akkdong/FlightComputer/doc/LCD/5inch-HDMI-LCD-B-size.jpg

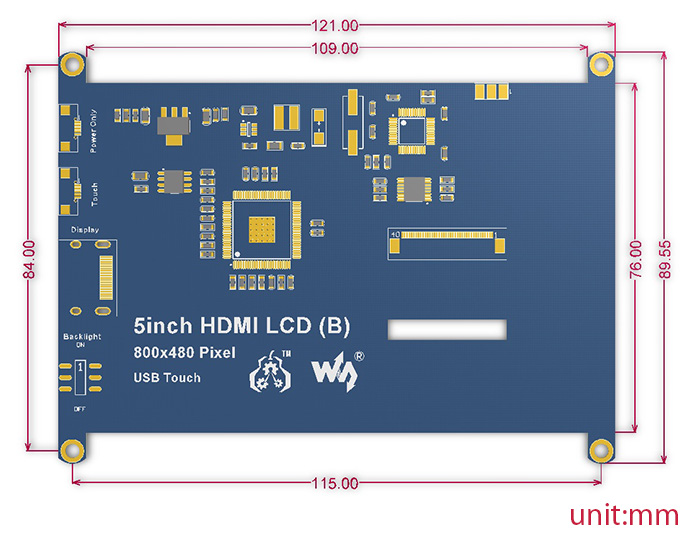
doc/LCD/5inch-HDMI-LCD-B-size.jpg
