akkdong/FlightComputer/hw/case/FlightComputer-Extra-Outline.dxf

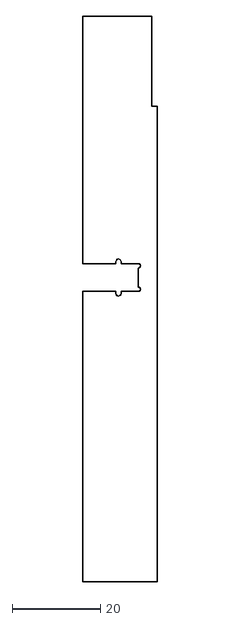
[picture p28: CAD file, 2020-10-16]
hw/case/FlightComputer-Extra-Outline.dxf
16.9 x 128.0
