akkdong/FlightComputer/hw/case/FlightComputer-Keypad-Parts.dxf

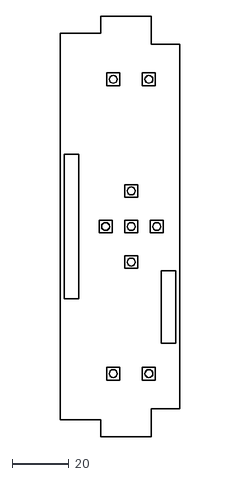
[picture p29: CAD file, 2020-10-16]
hw/case/FlightComputer-Keypad-Parts.dxf
42.0 x 148.0
