akkdong/FlightComputer/hw/case/FlightComputer-Dimension-Main.pdf

0 118.96 32.6

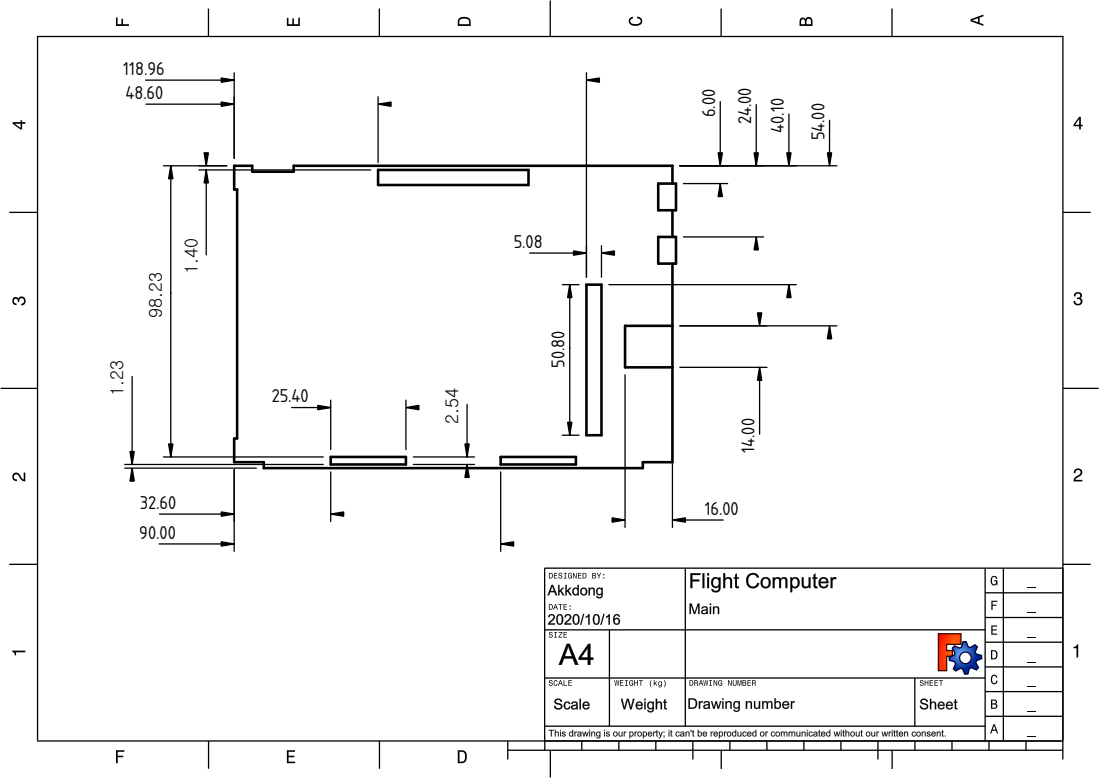
[picture p48: page 1]
