akkdong/FlightComputer/hw/case/FlightComputer-Dimension-Extra.pdf

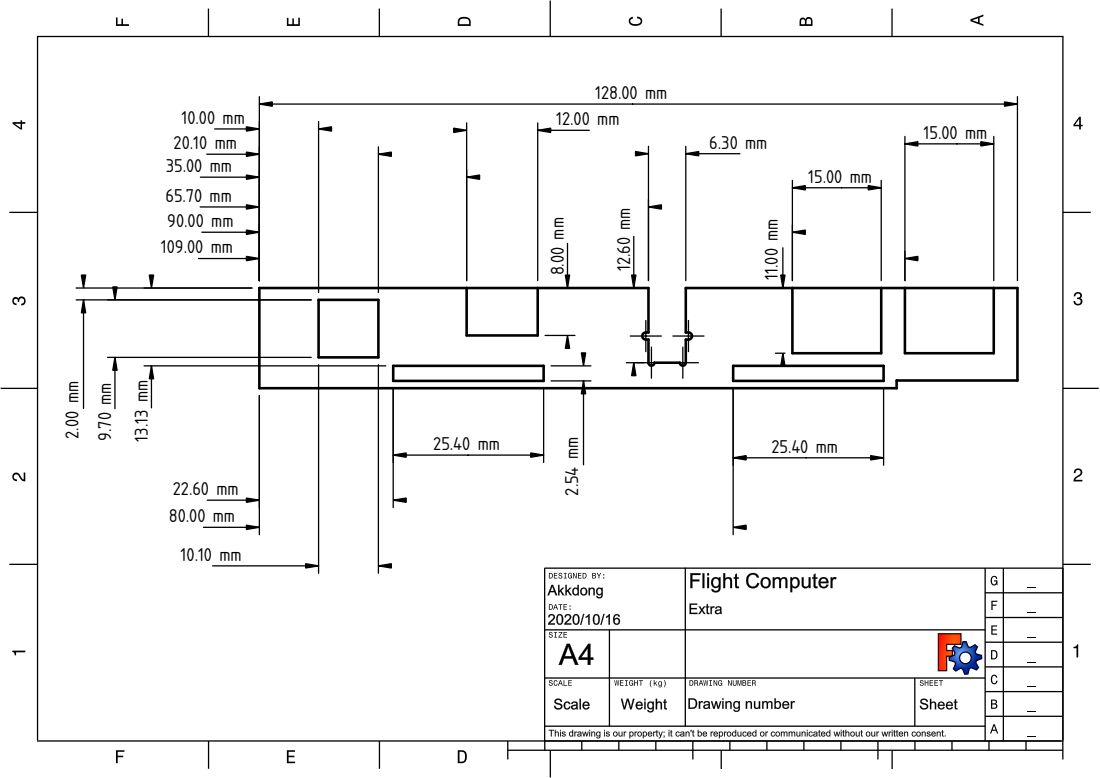
[picture p49: page 1]
