akkdong/FlightComputer/hw/case/FlightComputer-Dimension-Keypad.pdf

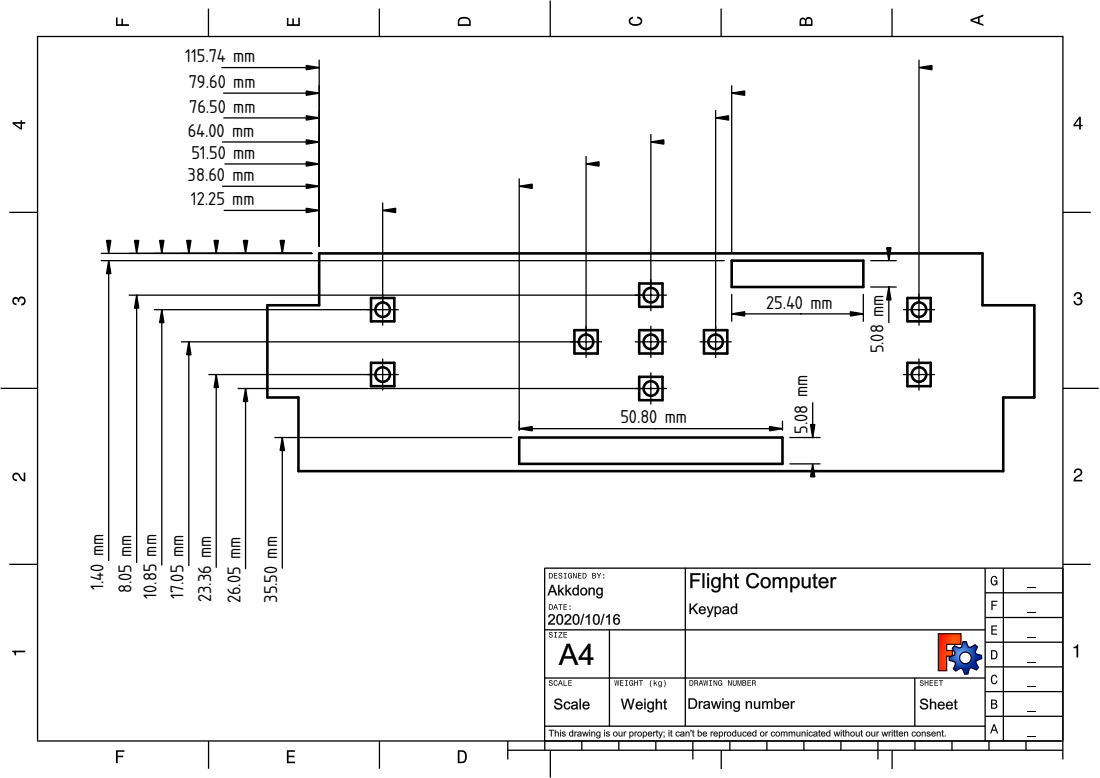
[picture p50: page 1]
