akkdong/FlightComputer/doc/LCD/5inch-hdmi-lcd-&-5inch-hdmi-lcd-b-panel-dimension.pdf

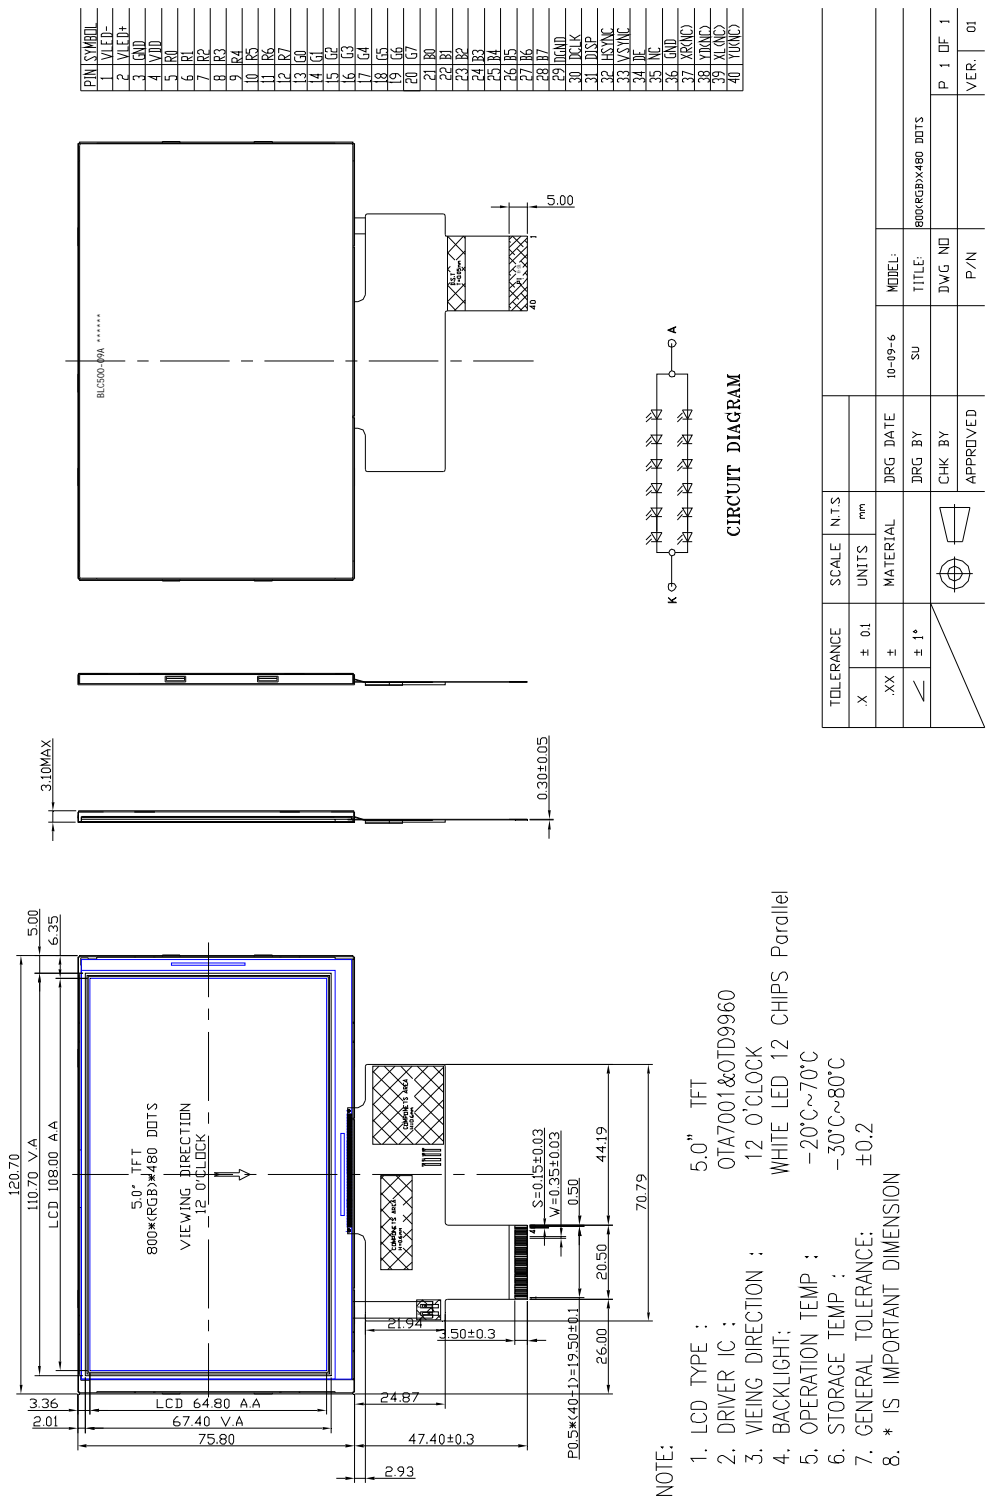
[picture p51: page 1]
BLC500-09A ******
