akkdong/FlightComputer/hw/rev1/FlightComputer/FlightComputer.pdf

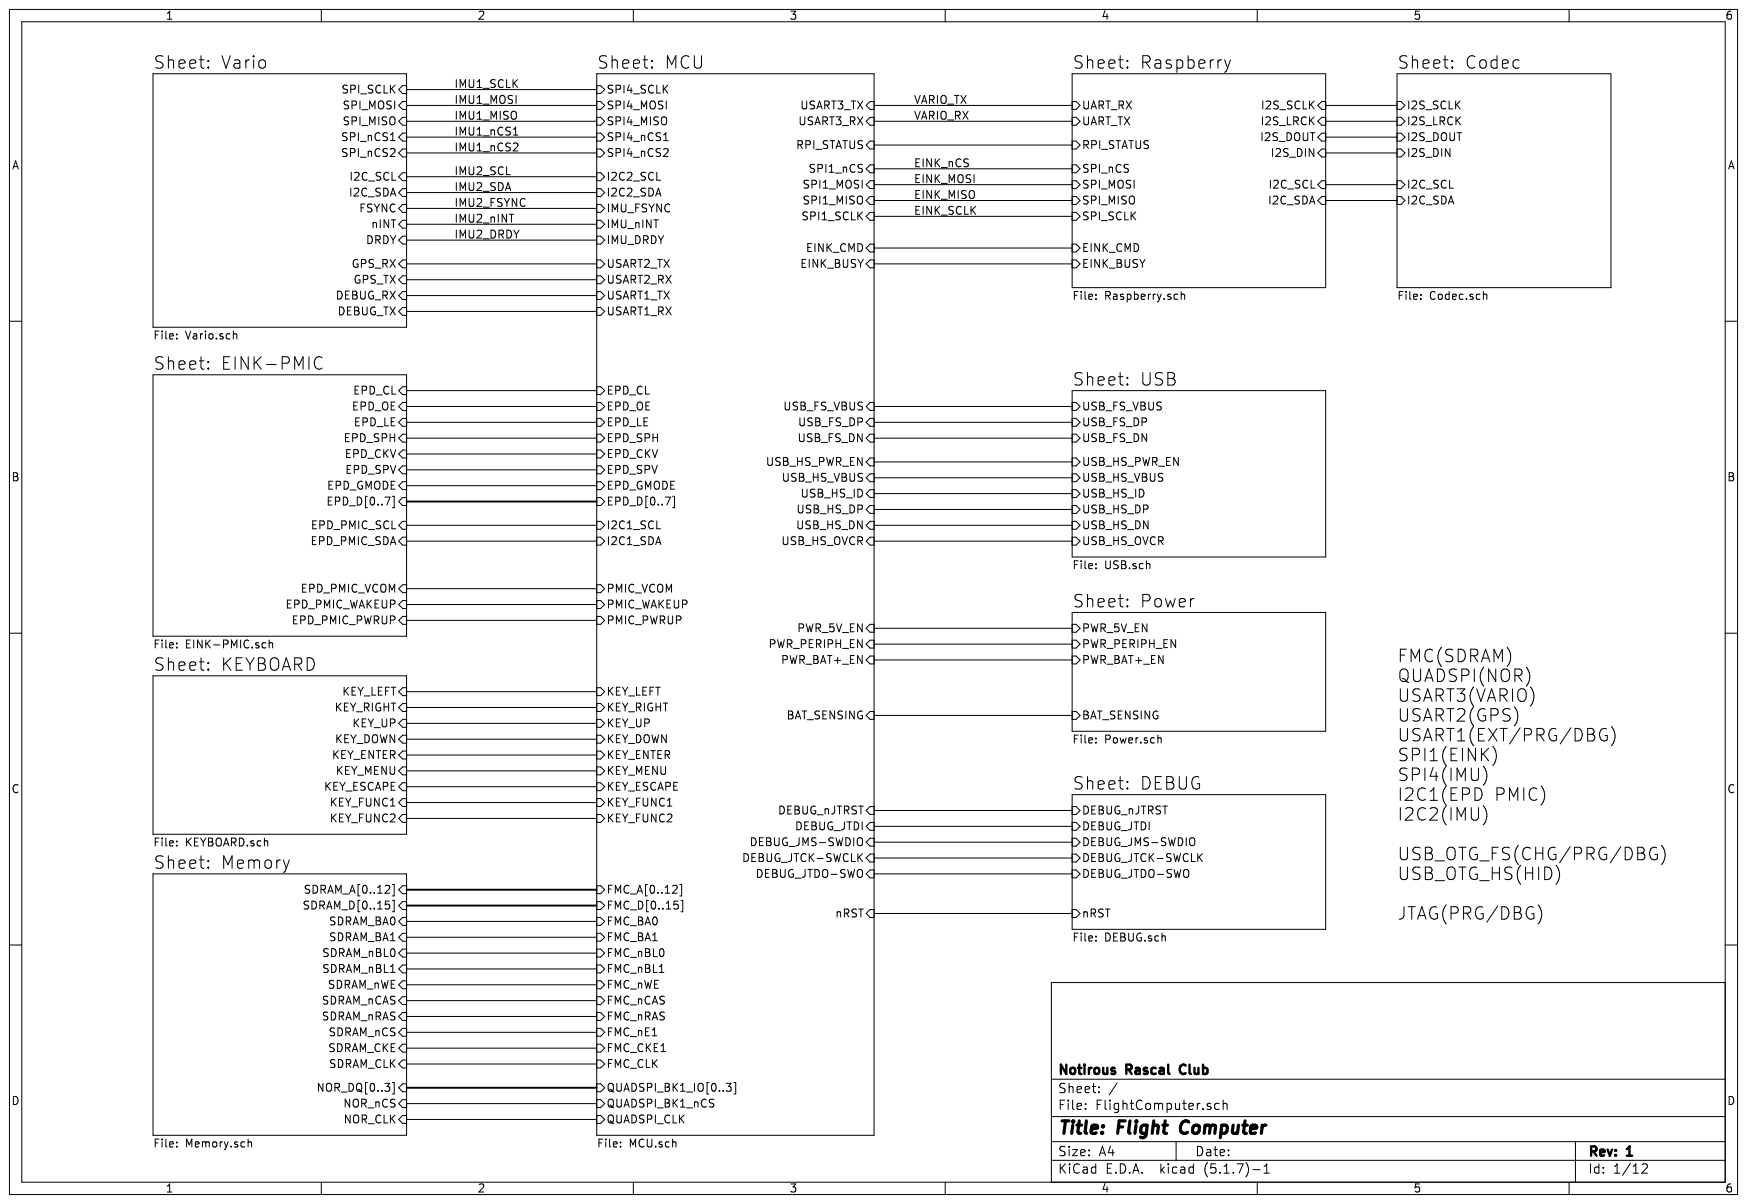
[picture p52: page 1]

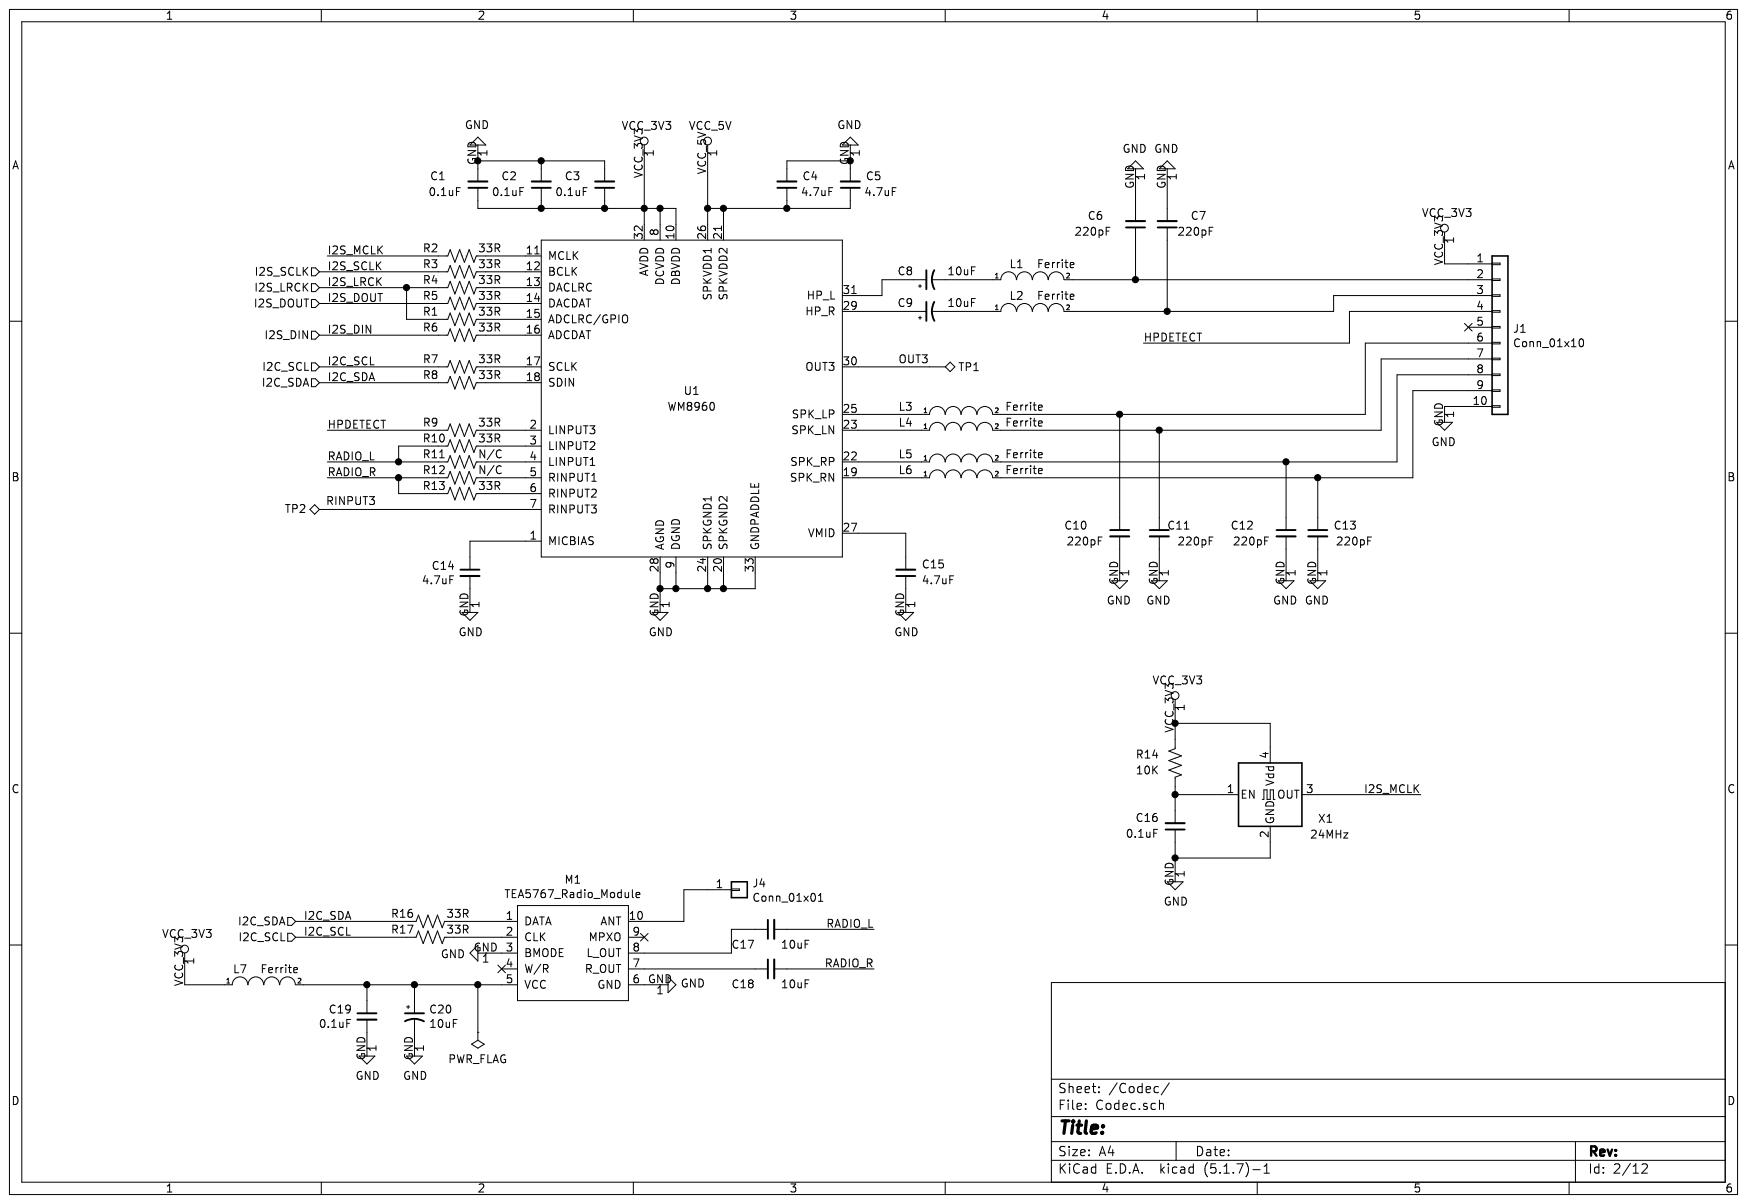
[picture p53: page 2]

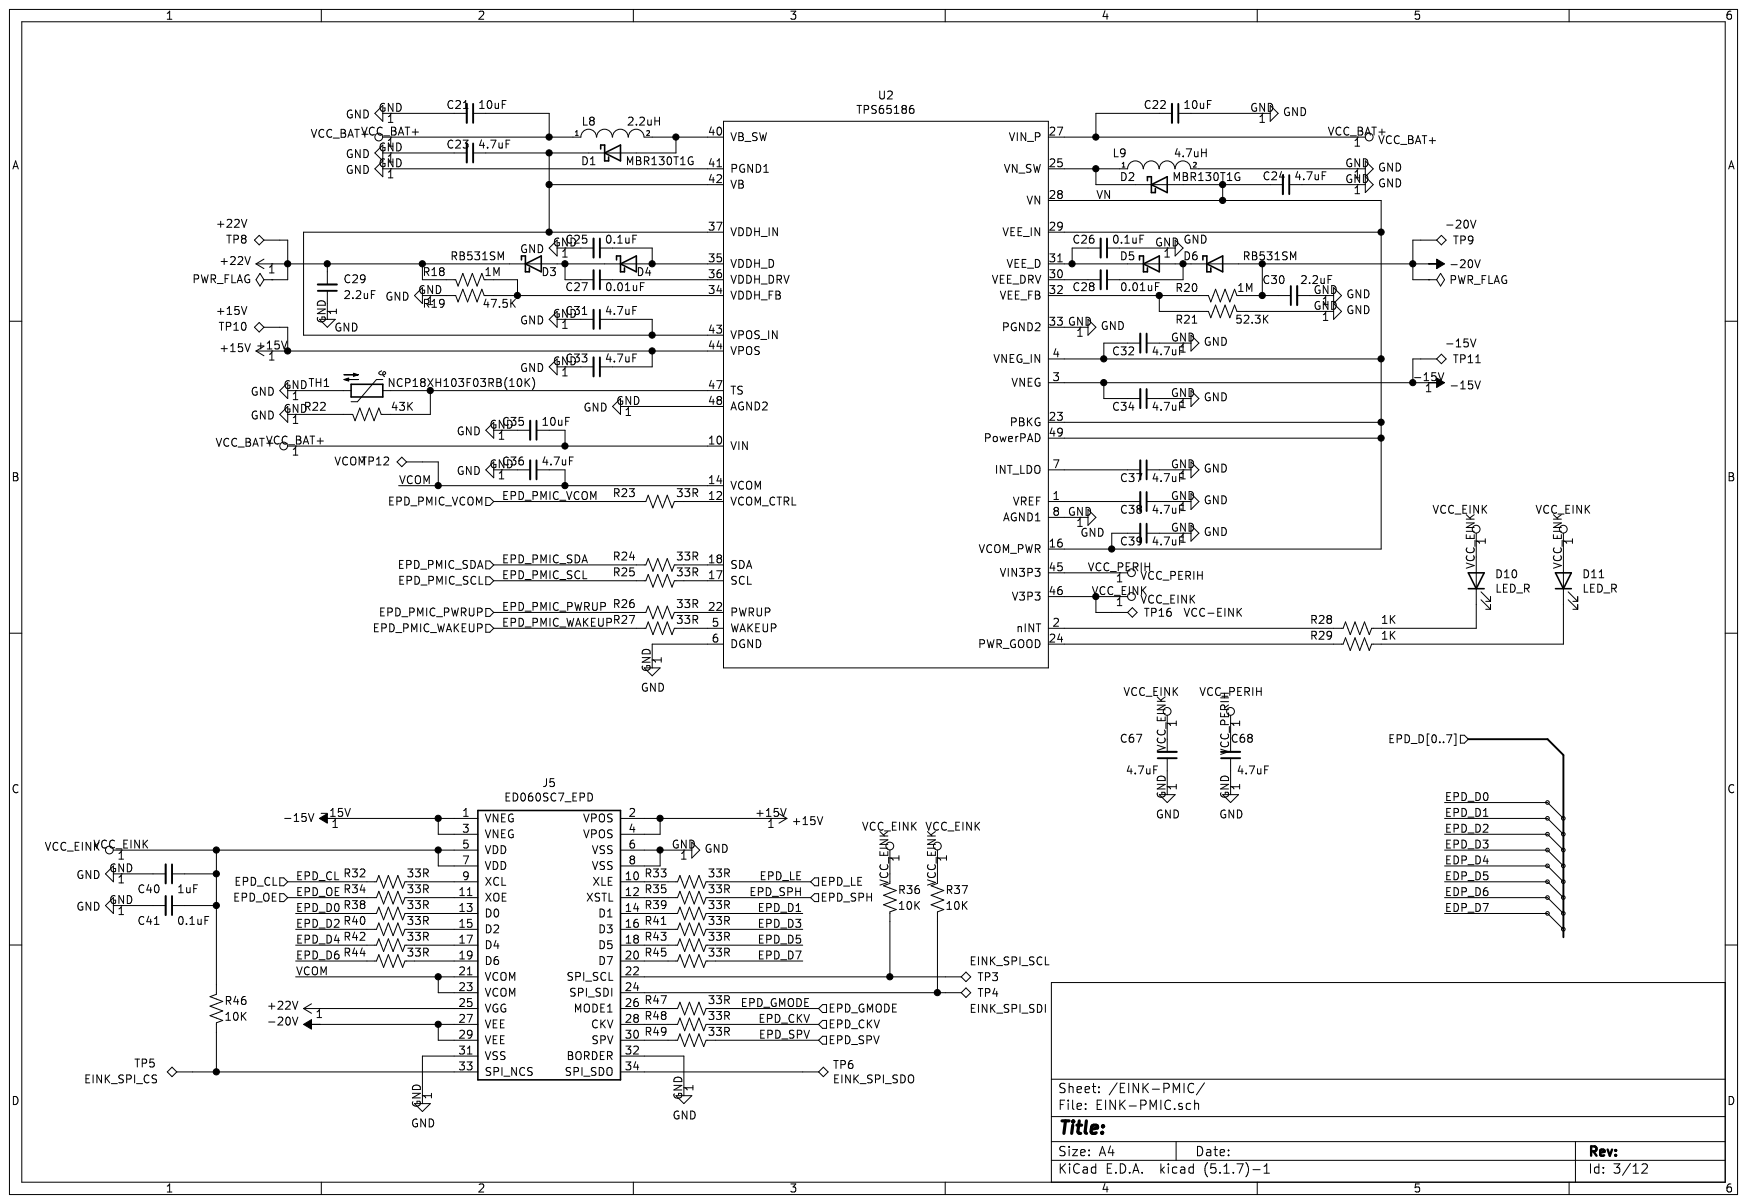
[picture p54: page 3]

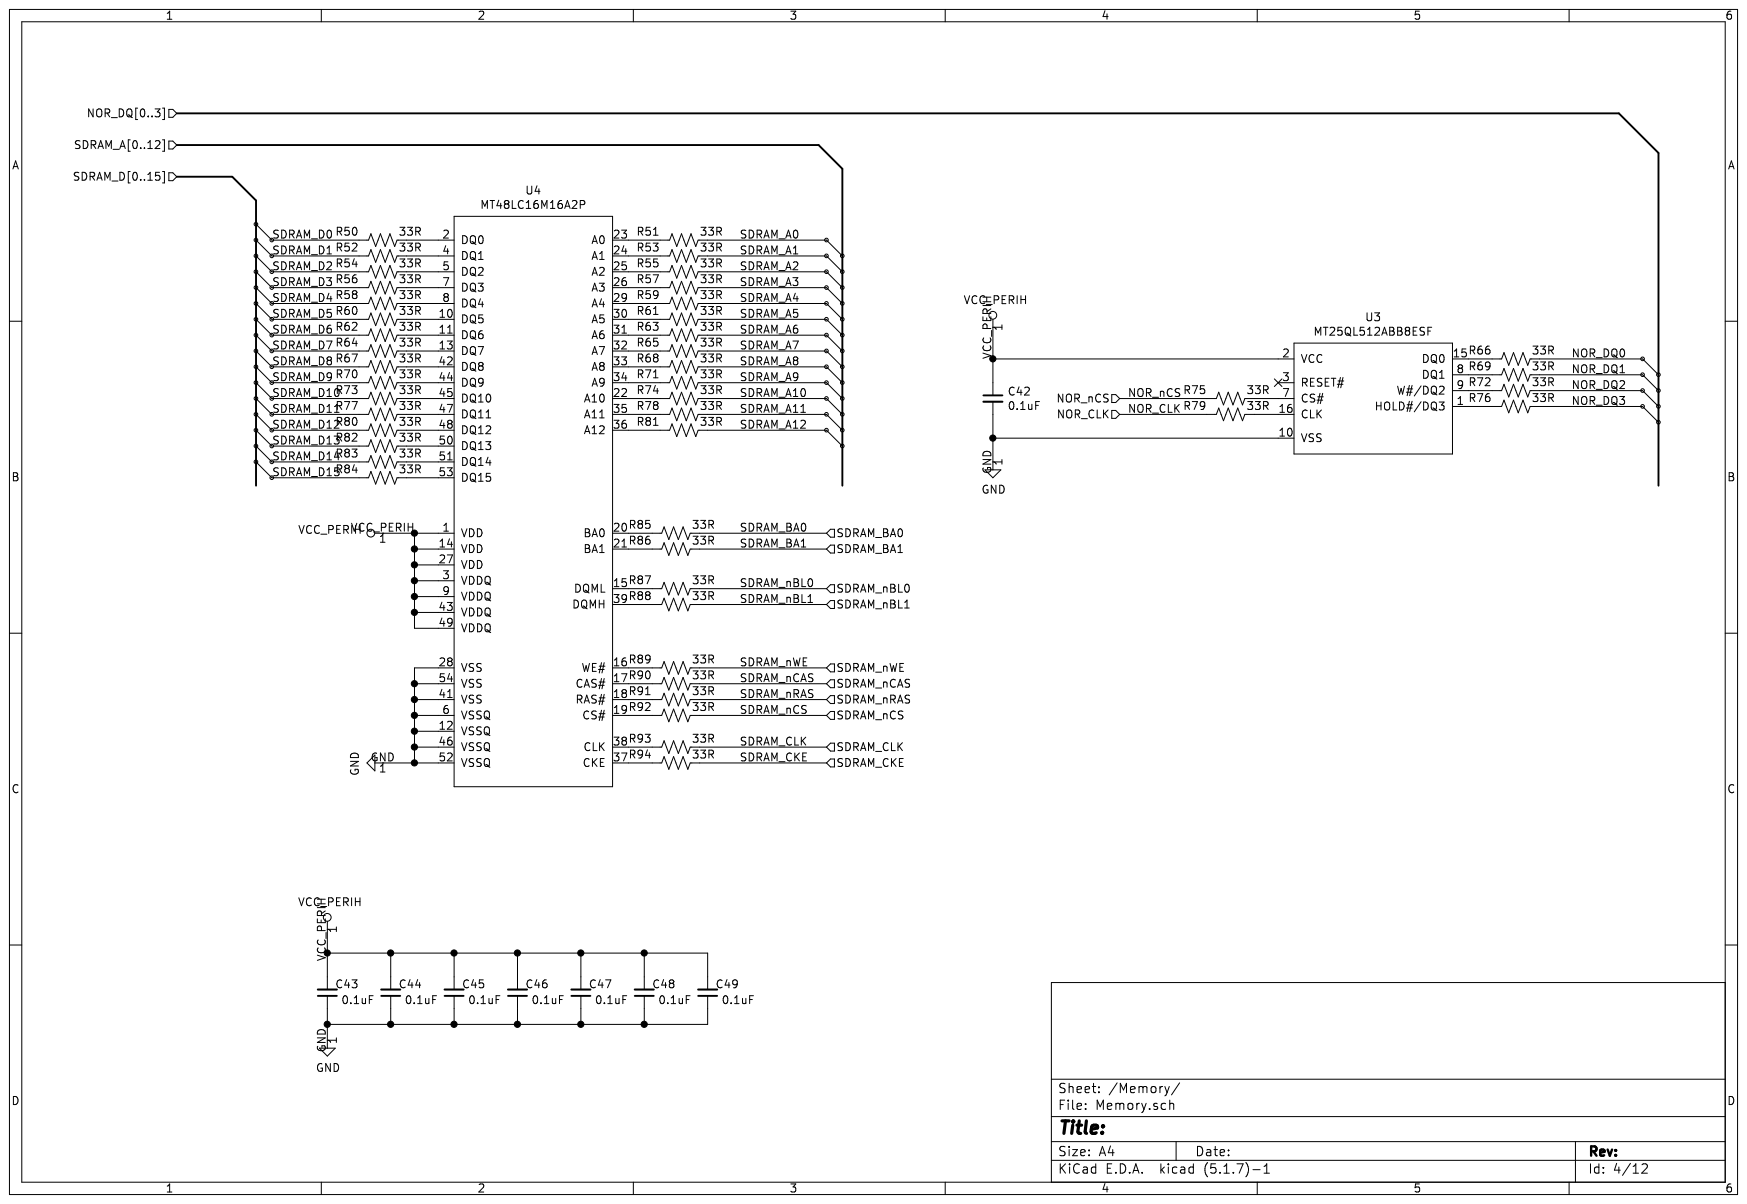
[picture p55: page 4]

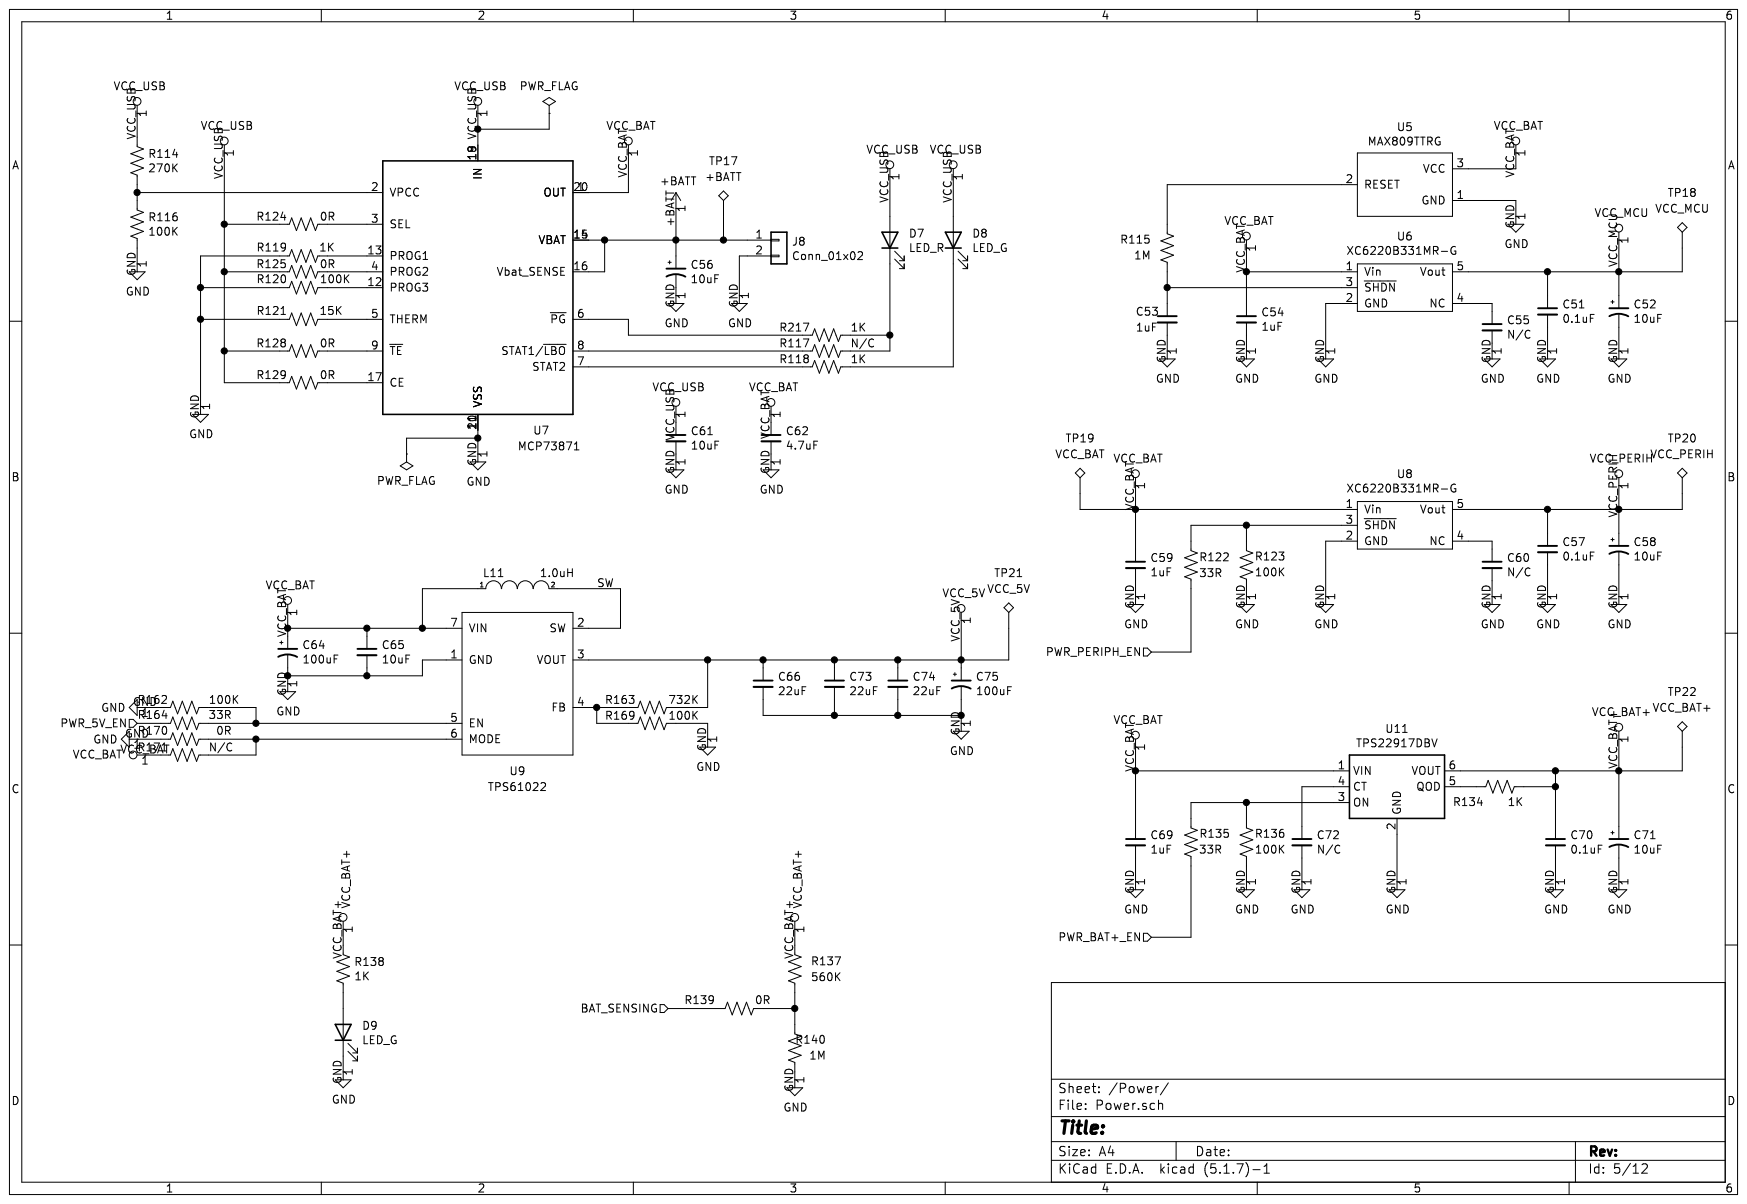
[picture p56: page 5]

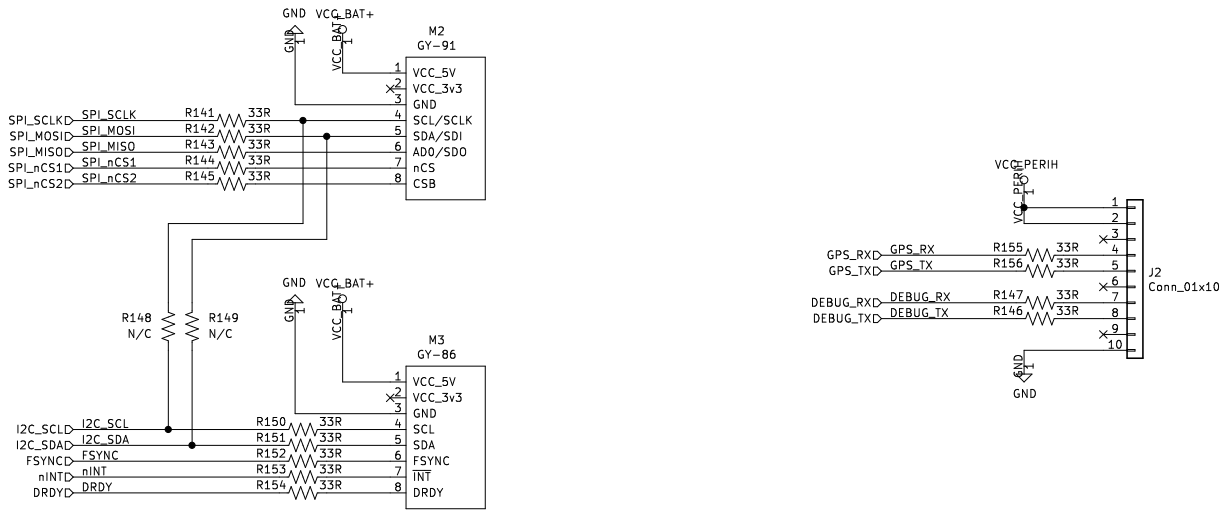
[picture p57: page 6]

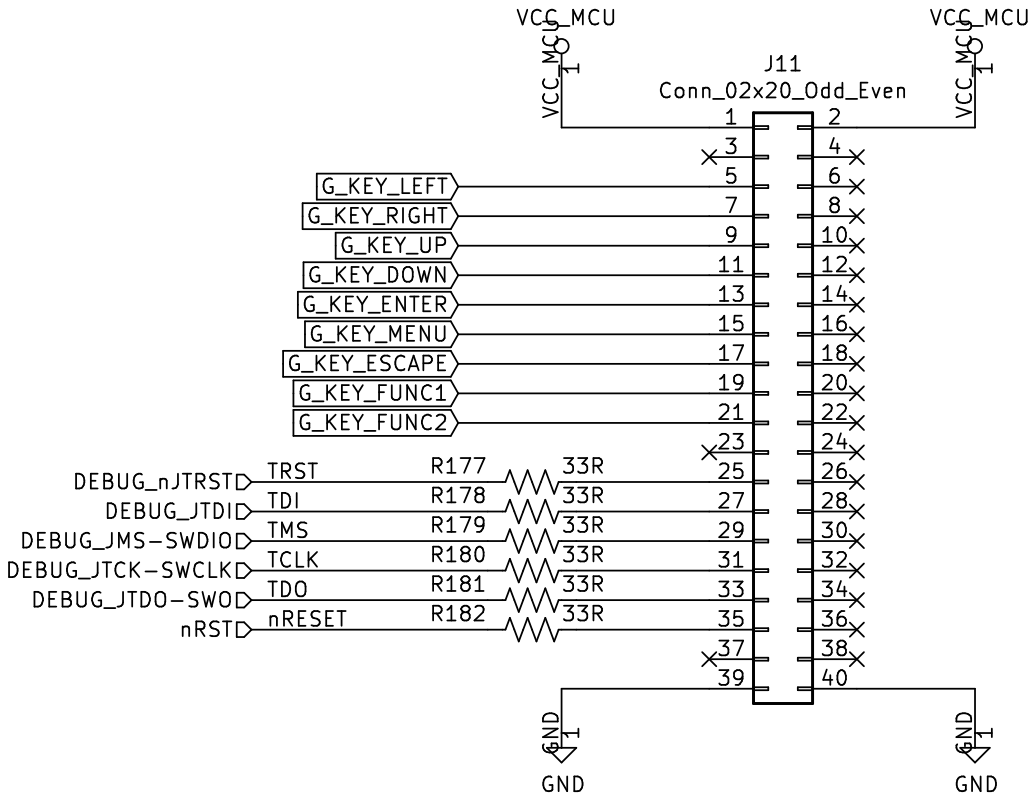
[picture p58: page 7]

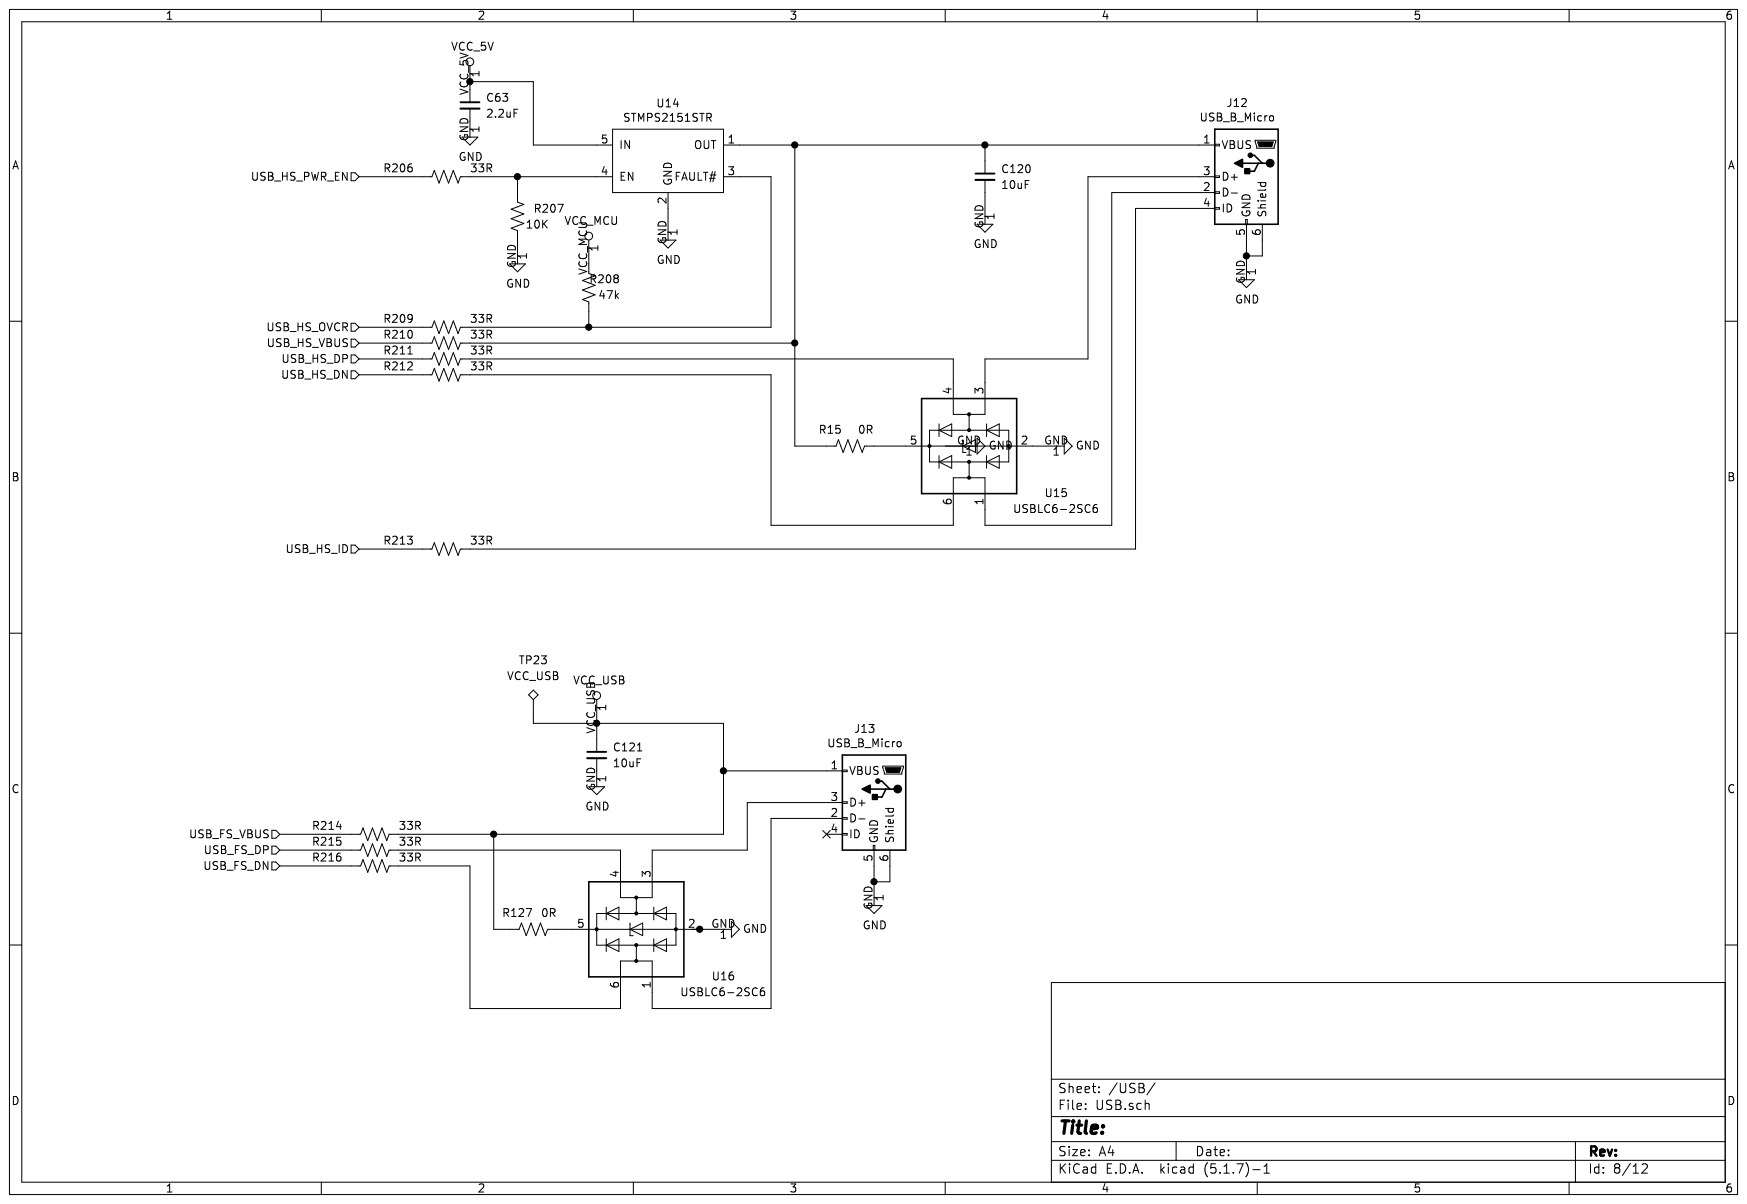
[picture p59: page 8]

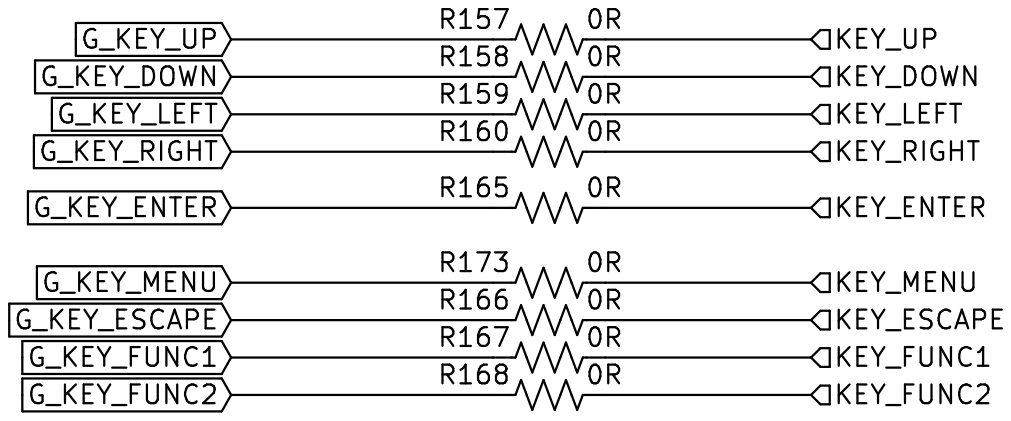
[picture p60: page 9]

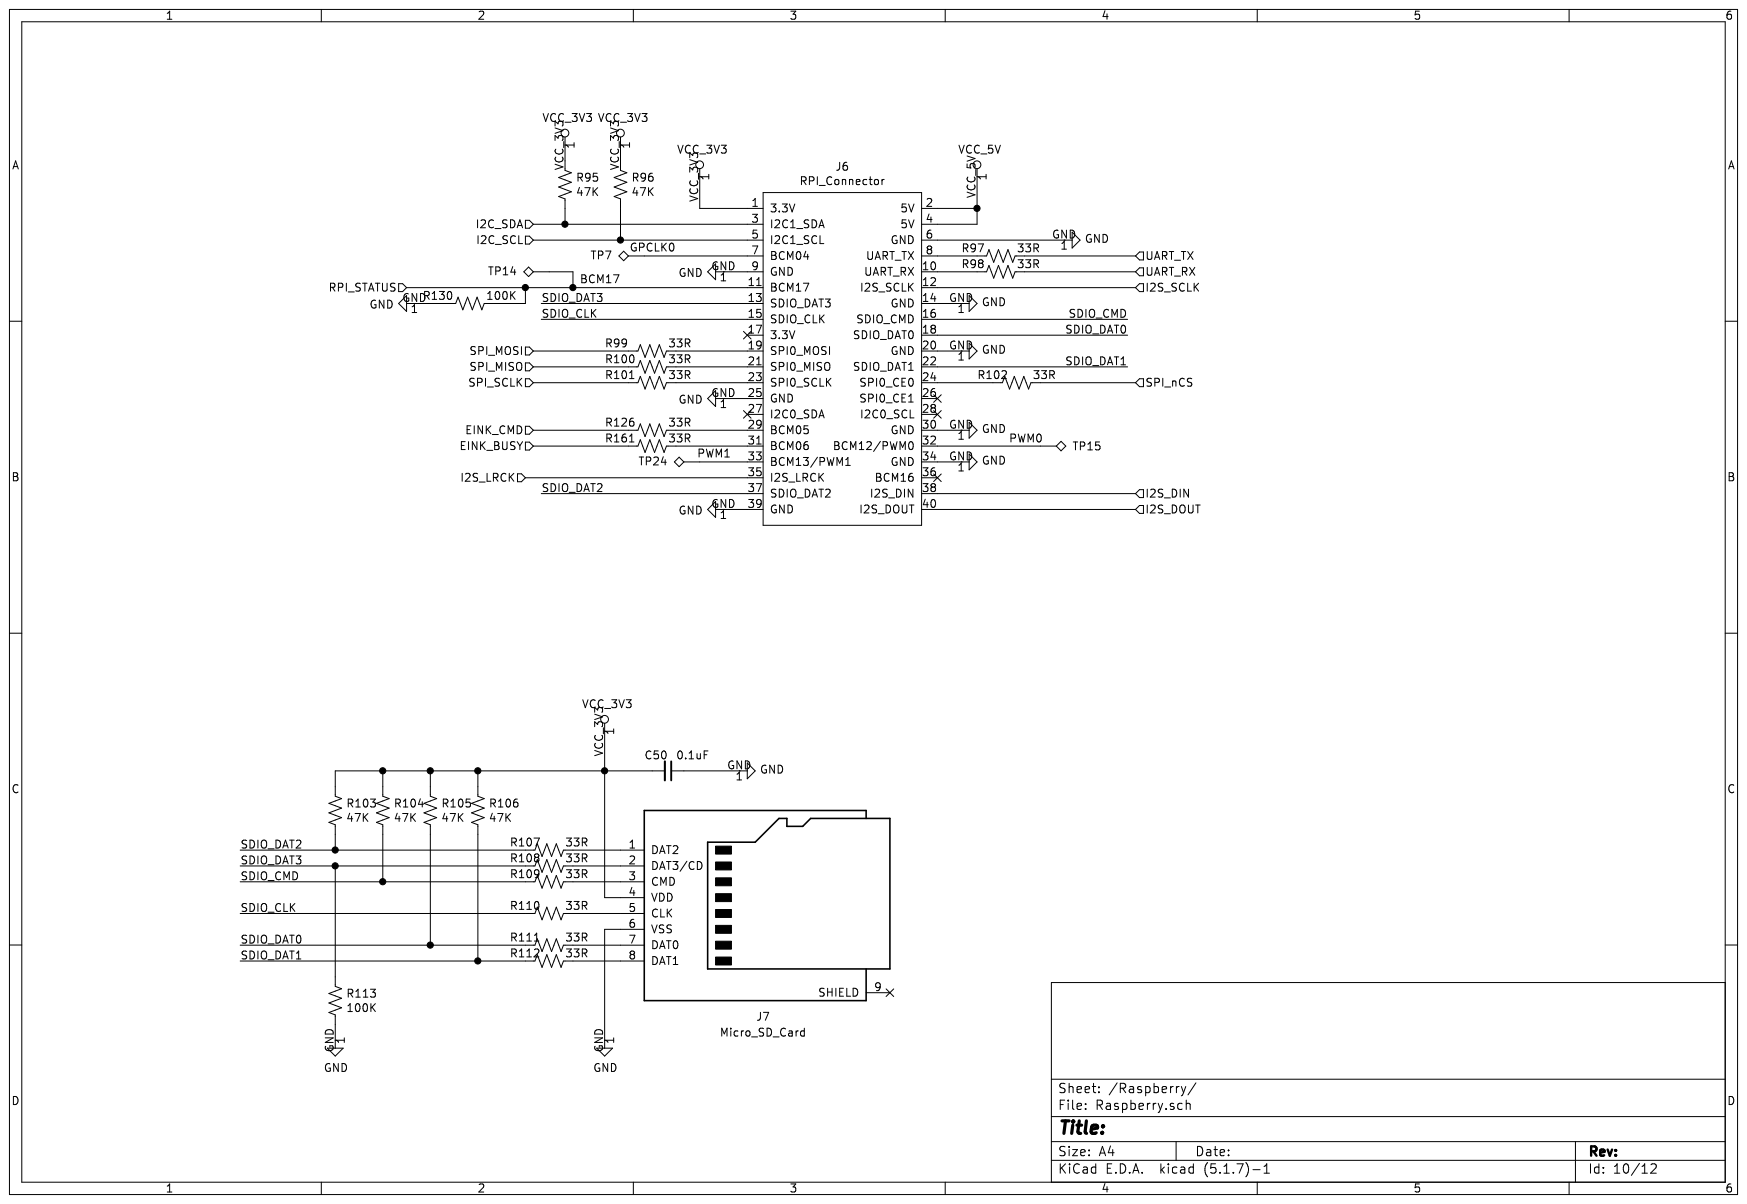
[picture p61: page 10]

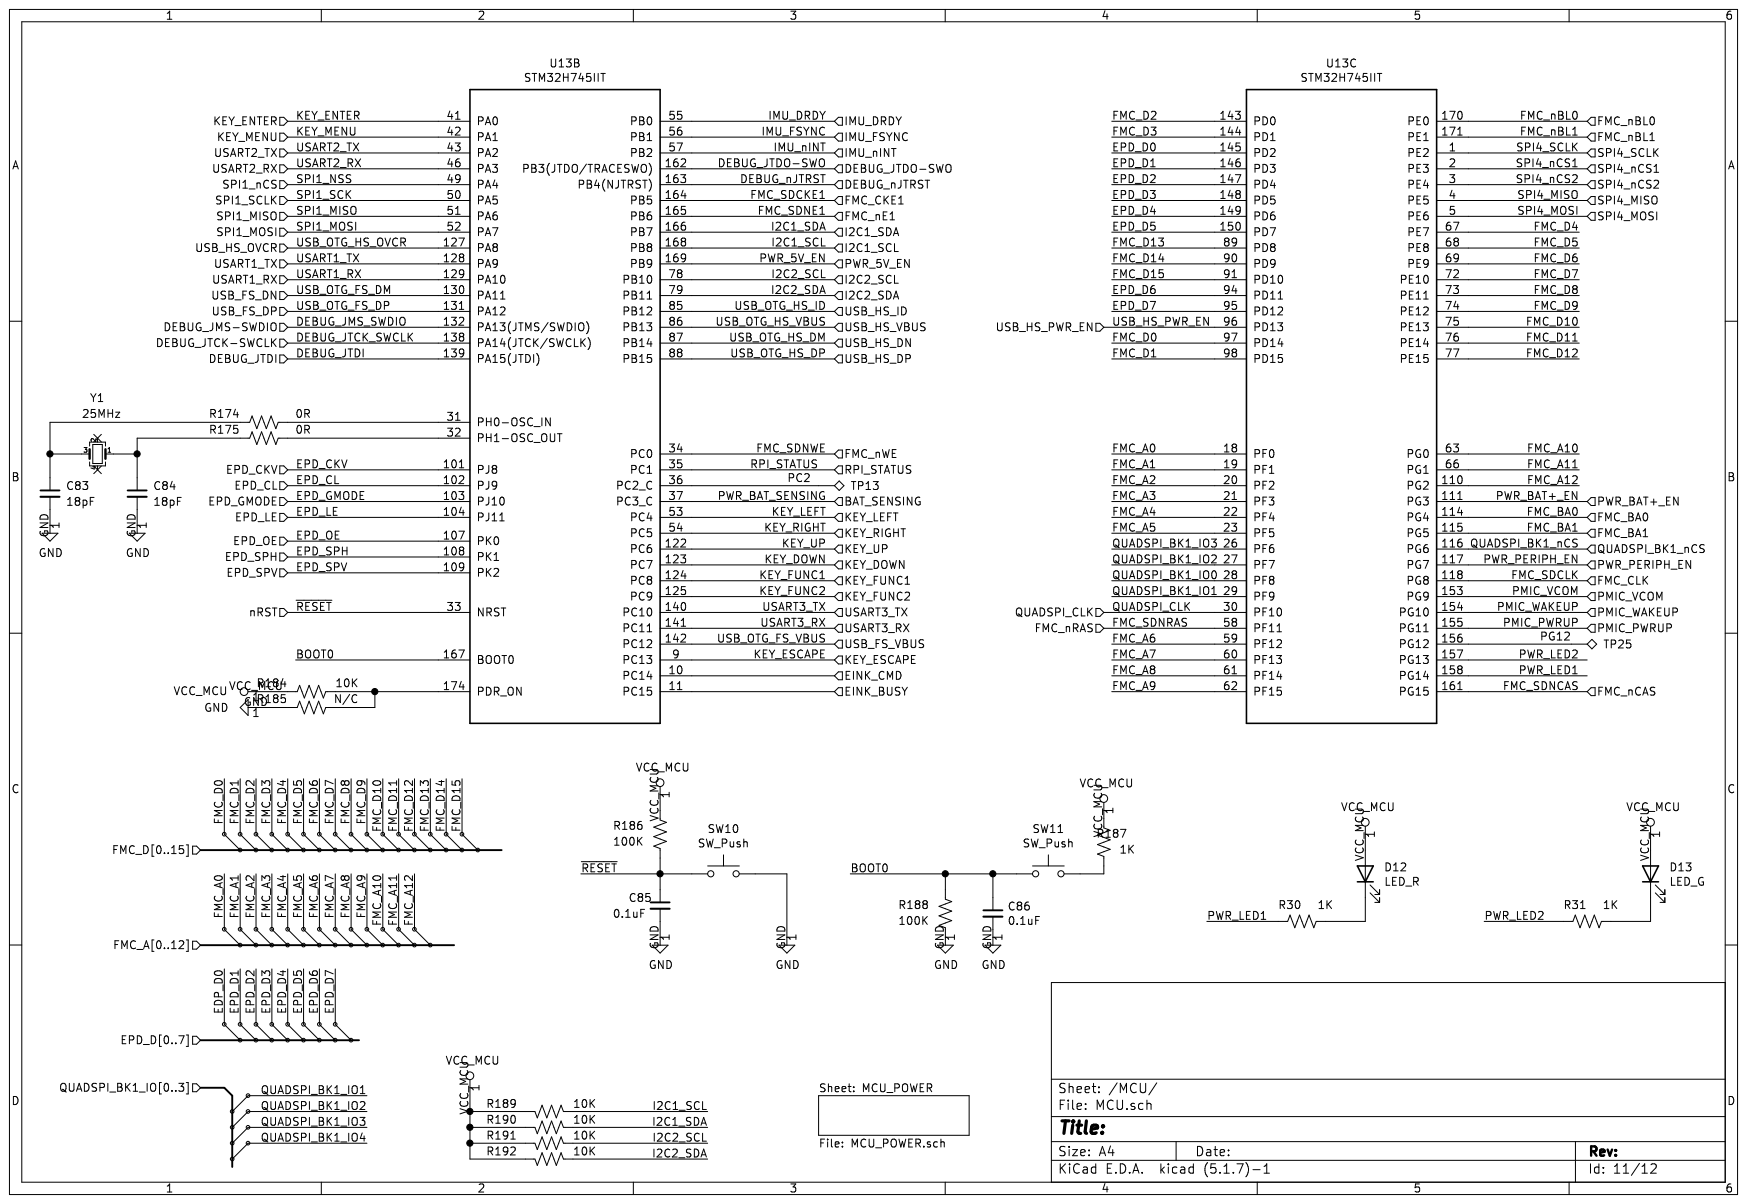
[picture p62: page 11]

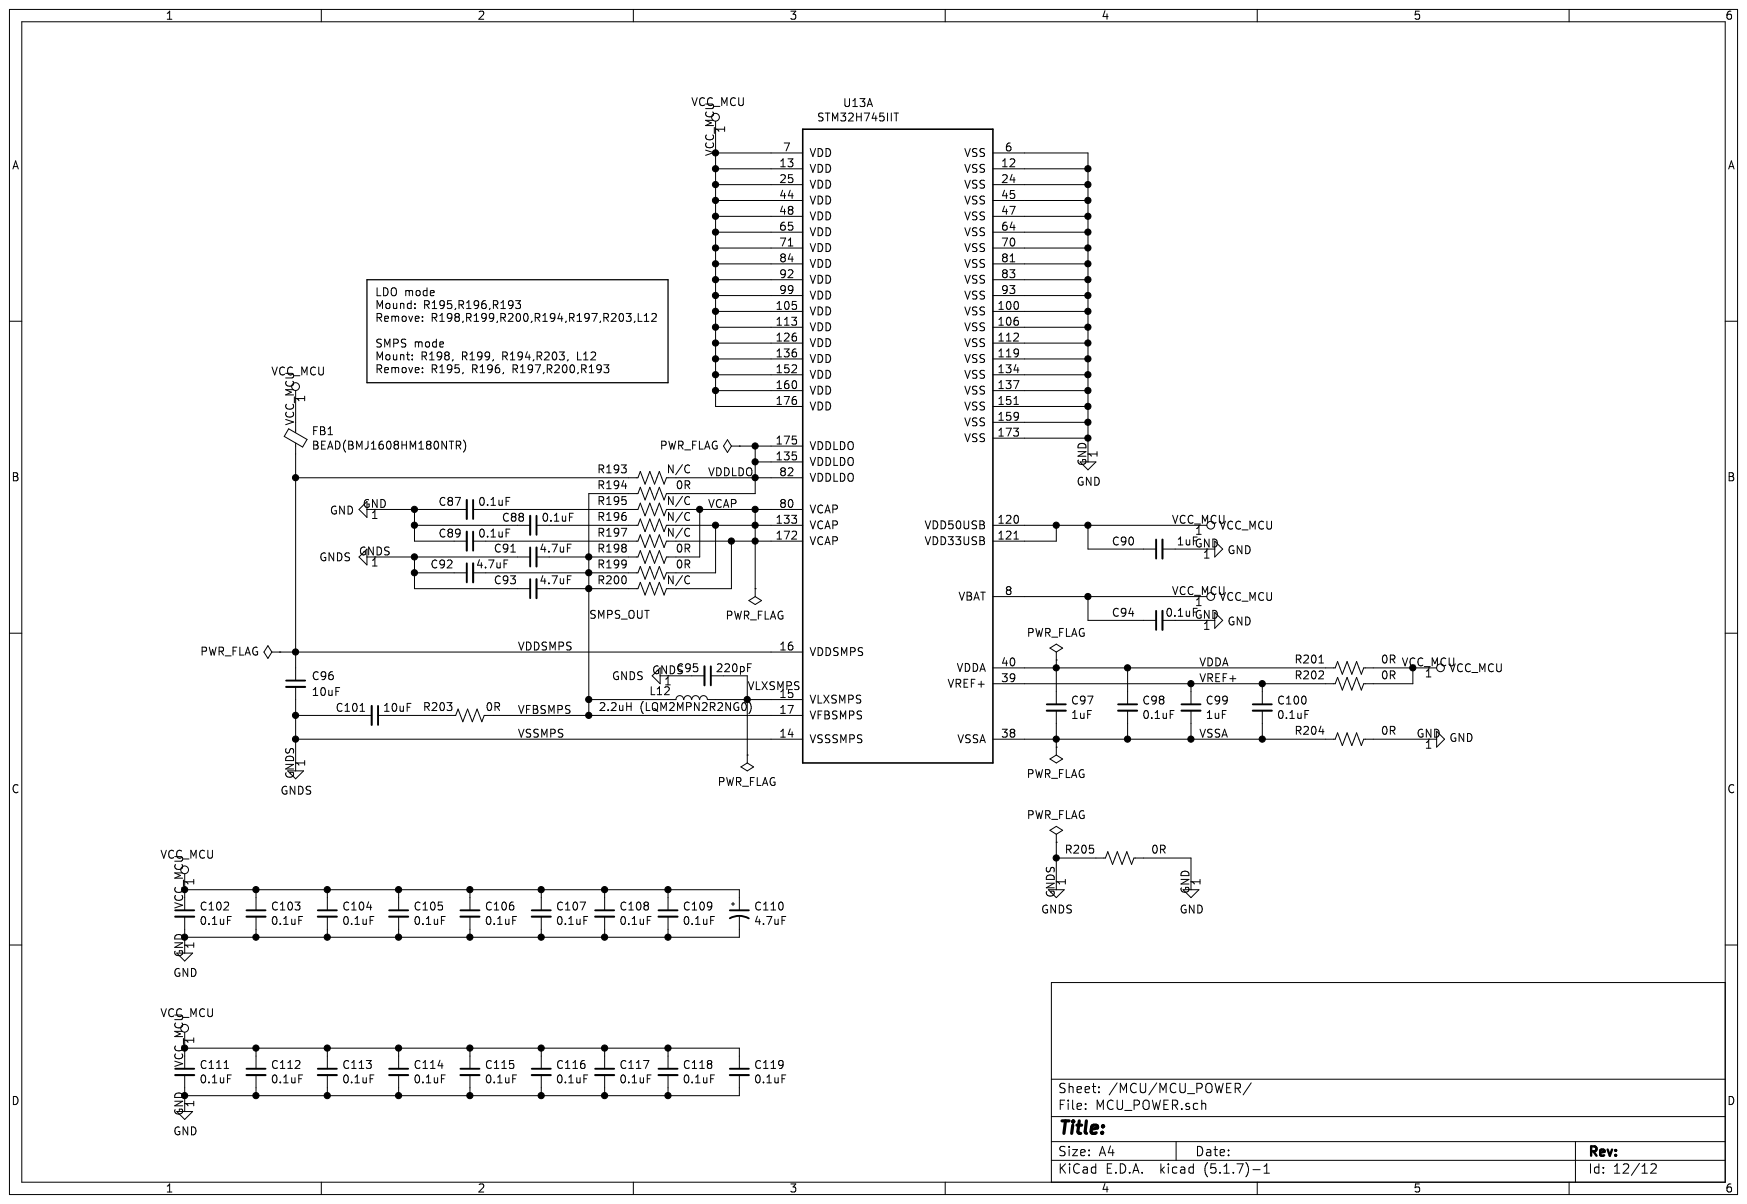
[picture p63: page 12]
