akkdong/FlightComputer/hw/rev1/FlightComputer-Extra/FlightComputer-Extra.pdf

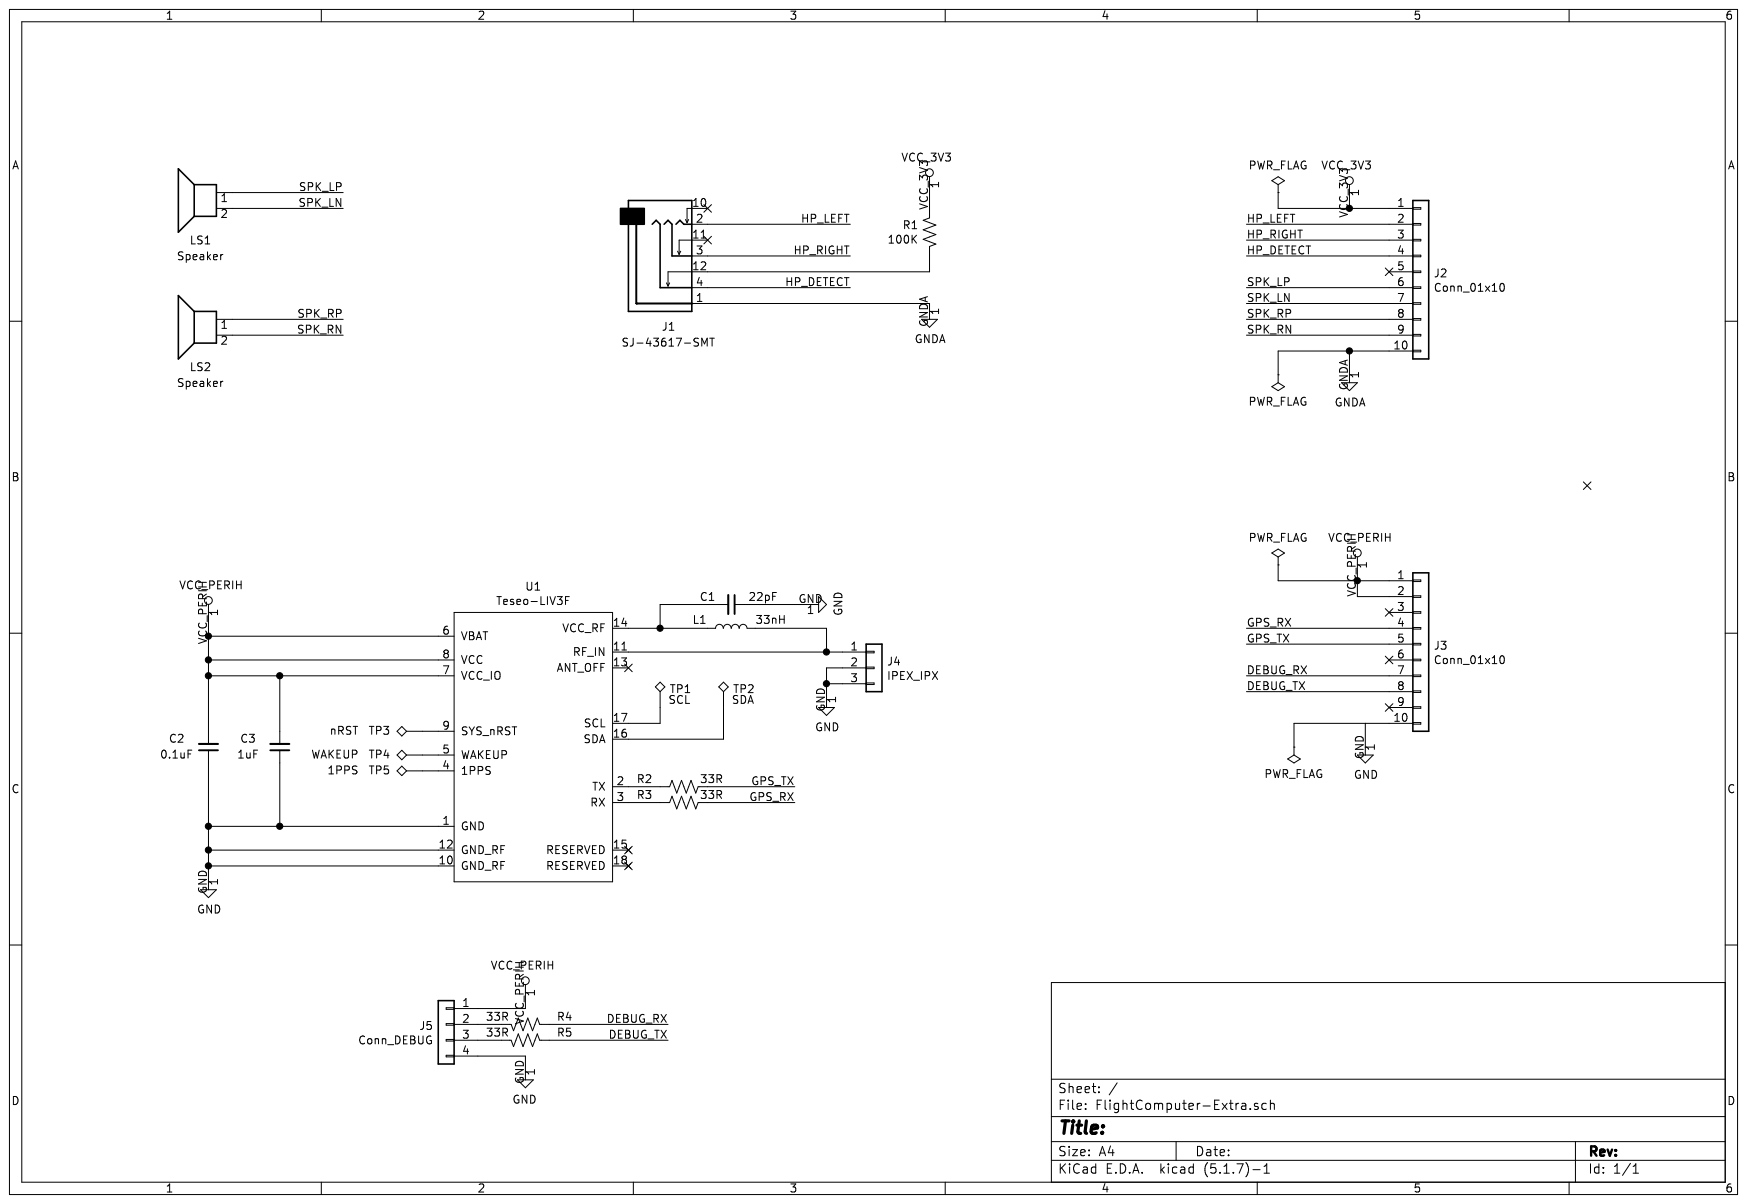
[picture p64: page 1]
