akkdong/FlightComputer/hw/rev1/FlightComputer-Keypad/FlightComputer-Keypad.pdf

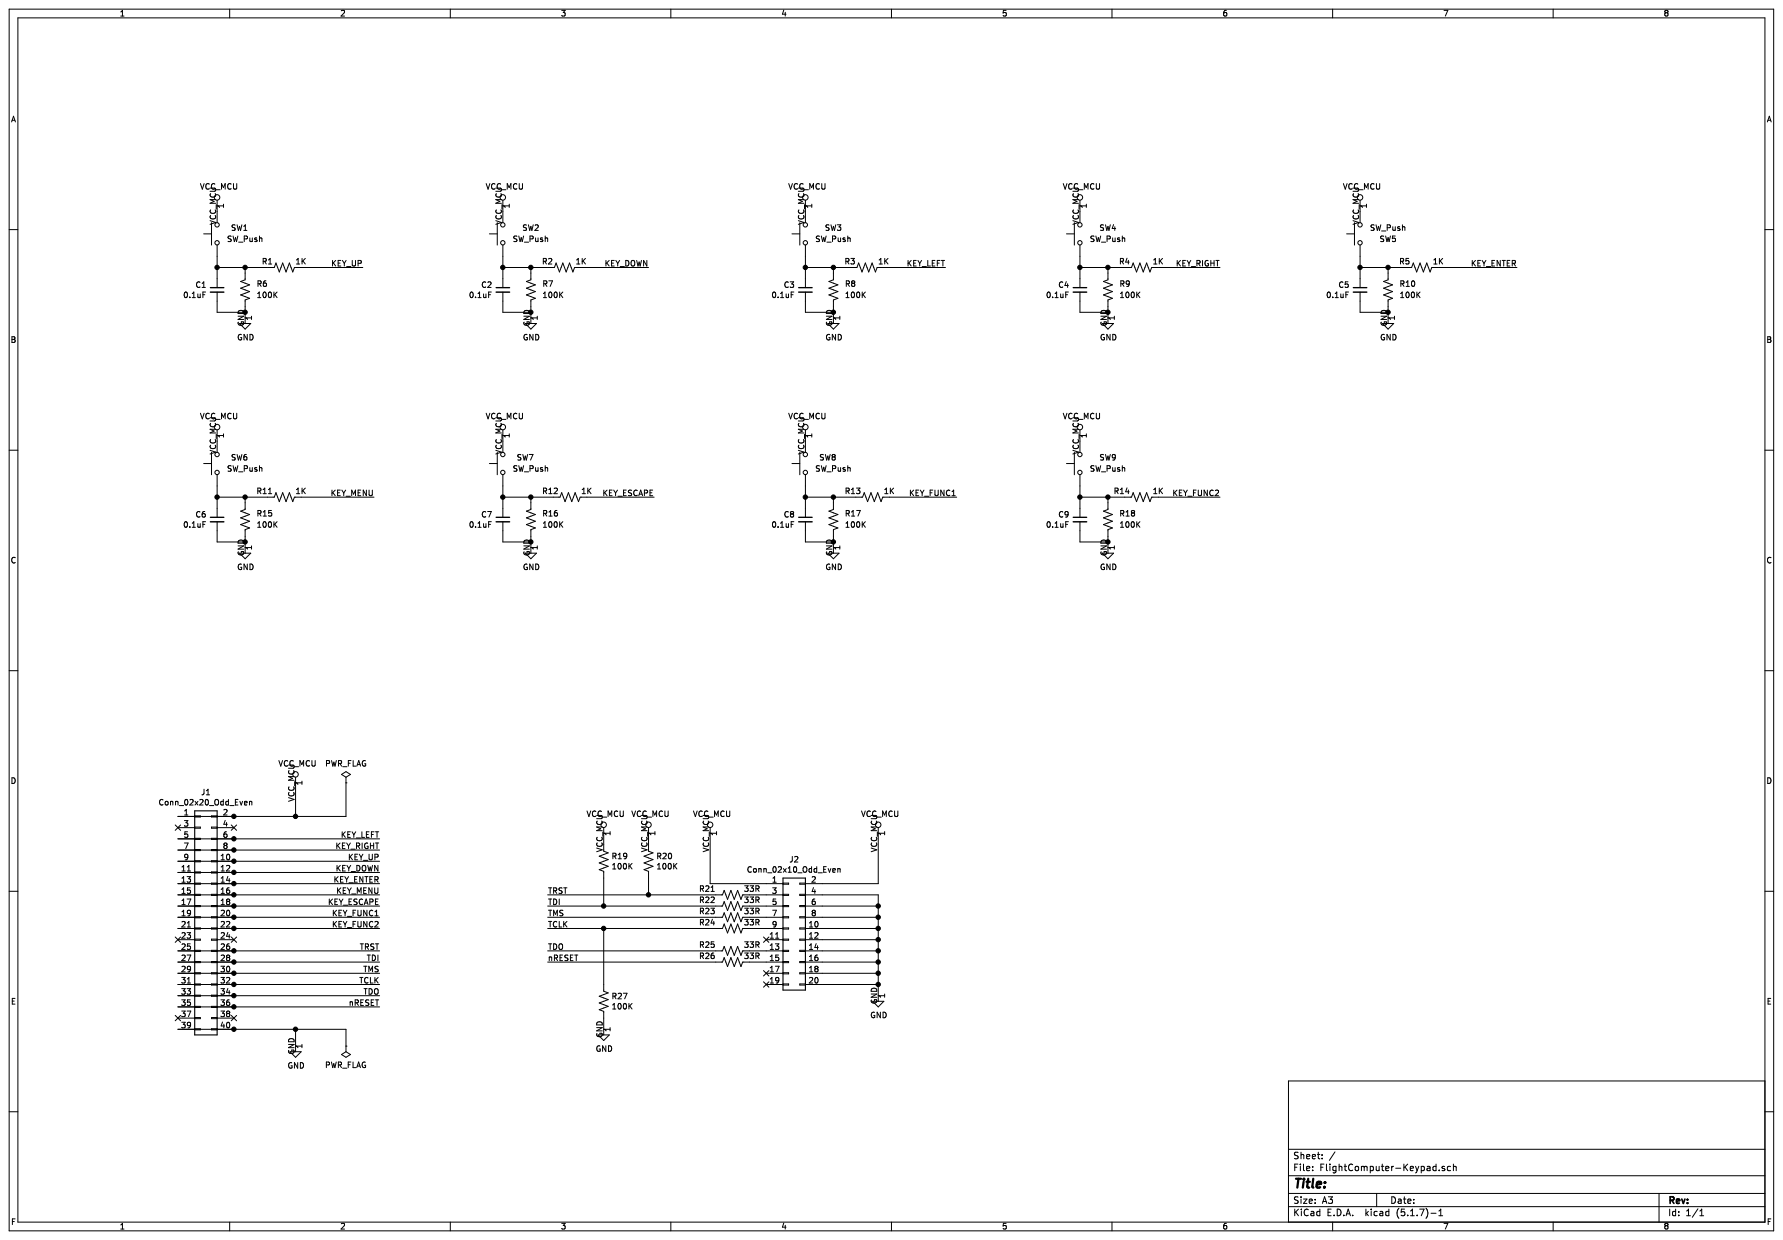
[picture p65: page 1]
