akkdong/FlightComputer/src/FlightComputer/CM7/Core/Inc/FlightComputer.h

/*
 * FlightComputer.h
 *
 *  Created on: 2021. 12. 31.
 *      Author: akkdong
 */

#ifndef INC_FLIGHTCOMPUTER_H_
#define INC_FLIGHTCOMPUTER_H_

#include "Arduino.h"
#include "SPI/SPIClassEx.h"
#include "EPD/EPaperController.h"
#include "EPD/EPaperDisplay.h"
#include "KeyPad/KeyPad.h"

#include "common.h"



/////////////////////////////////////////////////////////////////////////////////////
// class FlightComputer

class FlightComputer
{
public:
	FlightComputer();

	enum Event {
		VARIO_UPDATED,
		GPS_UPDATED
	};

public:
	//
	void 				setup();
	void 				loop();

	//
	void				OnUpdateVario();
	void				OnUpdateGPS();

protected:
	void				standby();

	//
	void				procDebugShell();
	void				procInterProcess();
	void				procKeyboard();
#if SUPPORT_LVGL
	void				procLVGL();
#endif

	//
	void				updateScreen(bool fast = true);

	//
	void				drawStandby();
	void				drawVarioState();

public:
	static bool			flash_ok;
	static bool			sdram_ok;

protected:
// 	FileSystem 			fs;
// 	EPapper				paper;
//  MonitorManager		mm;

	SPIClassEx			spi1;
	KeyPad				keyPad;
	//EPaperController	epdCont;
	EPaperDisplay		epdDisp;

	uint8_t				line_buf[256];
	int					line_len;

	uint8_t				disp_buf[0x7FF];
	int					disp_front, disp_rear;


	//
	lwrb_t* 			rb_cm4_to_cm7;
	lwrb_t* 			rb_cm7_to_cm4;

	volatile vario_t*	varioState;

	//
	uint32_t			displayUpdateTick;
	int					displayUpdateCount;
	int					enterStandby;
};


#endif /* INC_FLIGHTCOMPUTER_H_ */
