akkdong/FlightComputer/src/ExternalLoader/CM7/Core/Src/quadspi.c

/**
  ******************************************************************************
  * @file    quadspi.c
  * @brief   This file provides code for the configuration
  *          of the QUADSPI instances.
  ******************************************************************************
  * @attention
  *
  * <h2><center>&copy; Copyright (c) 2020 STMicroelectronics.
  * All rights reserved.</center></h2>
  *
  * This software component is licensed by ST under BSD 3-Clause license,
  * the "License"; You may not use this file except in compliance with the
  * License. You may obtain a copy of the License at:
  *                        opensource.org/licenses/BSD-3-Clause
  *
  ******************************************************************************
  */

/* Includes ------------------------------------------------------------------*/
#include "quadspi.h"

/* USER CODE BEGIN 0 */
static uint8_t QSPI_WriteEnable(void);
static uint8_t QSPI_AutoPollingMemReady(uint32_t Timeout);
static uint8_t QSPI_Configuration(void);
static uint8_t QSPI_ResetChip(void);
/* USER CODE END 0 */

QSPI_HandleTypeDef hqspi;

/* QUADSPI init function */
void MX_QUADSPI_Init(void)
{

  hqspi.Instance = QUADSPI;
  hqspi.Init.ClockPrescaler = 1;
  hqspi.Init.FifoThreshold = 1;
  hqspi.Init.SampleShifting = QSPI_SAMPLE_SHIFTING_NONE; // QSPI_SAMPLE_SHIFTING_NONE;
  hqspi.Init.FlashSize = 25;
  hqspi.Init.ChipSelectHighTime = QSPI_CS_HIGH_TIME_3_CYCLE;
  hqspi.Init.ClockMode = QSPI_CLOCK_MODE_0;
  hqspi.Init.FlashID = QSPI_FLASH_ID_1;
  hqspi.Init.DualFlash = QSPI_DUALFLASH_DISABLE;
  if (HAL_QSPI_Init(&hqspi) != HAL_OK)
  {
    Error_Handler();
  }

}

void HAL_QSPI_MspInit(QSPI_HandleTypeDef* qspiHandle)
{

  GPIO_InitTypeDef GPIO_InitStruct = {0};
  if(qspiHandle->Instance==QUADSPI)
  {
    /* QUADSPI clock enable */
    __HAL_RCC_QSPI_CLK_ENABLE();

    __HAL_RCC_GPIOF_CLK_ENABLE();
    __HAL_RCC_GPIOG_CLK_ENABLE();
    /**QUADSPI GPIO Configuration
    PF6     ------> QUADSPI_BK1_IO3
    PF7     ------> QUADSPI_BK1_IO2
    PF8     ------> QUADSPI_BK1_IO0
    PF9     ------> QUADSPI_BK1_IO1
    PF10     ------> QUADSPI_CLK
    PG6     ------> QUADSPI_BK1_NCS
    */
    GPIO_InitStruct.Pin = GPIO_PIN_6|GPIO_PIN_7|GPIO_PIN_10;
    GPIO_InitStruct.Mode = GPIO_MODE_AF_PP;
    GPIO_InitStruct.Pull = GPIO_NOPULL;
    GPIO_InitStruct.Speed = GPIO_SPEED_FREQ_VERY_HIGH;
    GPIO_InitStruct.Alternate = GPIO_AF9_QUADSPI;
    HAL_GPIO_Init(GPIOF, &GPIO_InitStruct);

    GPIO_InitStruct.Pin = GPIO_PIN_8|GPIO_PIN_9;
    GPIO_InitStruct.Mode = GPIO_MODE_AF_PP;
    GPIO_InitStruct.Pull = GPIO_NOPULL;
    GPIO_InitStruct.Speed = GPIO_SPEED_FREQ_VERY_HIGH;
    GPIO_InitStruct.Alternate = GPIO_AF10_QUADSPI;
    HAL_GPIO_Init(GPIOF, &GPIO_InitStruct);

    GPIO_InitStruct.Pin = GPIO_PIN_6;
    GPIO_InitStruct.Mode = GPIO_MODE_AF_PP;
    GPIO_InitStruct.Pull = GPIO_NOPULL;
    GPIO_InitStruct.Speed = GPIO_SPEED_FREQ_VERY_HIGH;
    GPIO_InitStruct.Alternate = GPIO_AF10_QUADSPI;
    HAL_GPIO_Init(GPIOG, &GPIO_InitStruct);

  }
}

void HAL_QSPI_MspDeInit(QSPI_HandleTypeDef* qspiHandle)
{

  if(qspiHandle->Instance==QUADSPI)
  {
    /* Peripheral clock disable */
    __HAL_RCC_QSPI_CLK_DISABLE();

    /**QUADSPI GPIO Configuration
    PF6     ------> QUADSPI_BK1_IO3
    PF7     ------> QUADSPI_BK1_IO2
    PF8     ------> QUADSPI_BK1_IO0
    PF9     ------> QUADSPI_BK1_IO1
    PF10     ------> QUADSPI_CLK
    PG6     ------> QUADSPI_BK1_NCS
    */
    HAL_GPIO_DeInit(GPIOF, GPIO_PIN_6|GPIO_PIN_7|GPIO_PIN_8|GPIO_PIN_9
                          |GPIO_PIN_10);

    HAL_GPIO_DeInit(GPIOG, GPIO_PIN_6);

  }
}

/* USER CODE BEGIN 1 */

/* QUADSPI init function */
uint8_t CSP_QUADSPI_Init(void) {
    //prepare QSPI peripheral for ST-Link Utility operations
	hqspi.Instance = QUADSPI;
    if (HAL_QSPI_DeInit(&hqspi) != HAL_OK) {
        return HAL_ERROR;
    }

    MX_QUADSPI_Init();

    if (QSPI_ResetChip() != HAL_OK) {
        return HAL_ERROR;
    }

    HAL_Delay(1);

    if (QSPI_AutoPollingMemReady(HAL_QPSI_TIMEOUT_DEFAULT_VALUE) != HAL_OK) {
        return HAL_ERROR;
    }

    if (QSPI_WriteEnable() != HAL_OK) {

        return HAL_ERROR;
    }

    if (QSPI_Configuration() != HAL_OK) {
        return HAL_ERROR;
    }

    if (QSPI_AutoPollingMemReady(HAL_QPSI_TIMEOUT_DEFAULT_VALUE) != HAL_OK) {
        return HAL_ERROR;
    }

    return HAL_OK;
}


uint8_t CSP_QSPI_Erase_Chip(void) {
    QSPI_CommandTypeDef sCommand;


    if (QSPI_WriteEnable() != HAL_OK) {
        return HAL_ERROR;
    }


    /* Erasing Sequence --------------------------------- */
    sCommand.Instruction = CHIP_ERASE_CMD;
    sCommand.InstructionMode = QSPI_INSTRUCTION_1_LINE;
    sCommand.AddressSize = QSPI_ADDRESS_32_BITS;
    sCommand.AlternateByteMode = QSPI_ALTERNATE_BYTES_NONE;
    sCommand.DdrMode = QSPI_DDR_MODE_DISABLE;
    sCommand.DdrHoldHalfCycle = QSPI_DDR_HHC_ANALOG_DELAY;
    sCommand.SIOOMode = QSPI_SIOO_INST_EVERY_CMD;
    sCommand.AddressMode = QSPI_ADDRESS_NONE;
    sCommand.Address = 0;
    sCommand.DataMode = QSPI_DATA_NONE;
    sCommand.DummyCycles = 0;


    if (HAL_QSPI_Command(&hqspi, &sCommand, HAL_QPSI_TIMEOUT_DEFAULT_VALUE)
        != HAL_OK) {
        return HAL_ERROR;
    }

    if (QSPI_AutoPollingMemReady(QUADSPI_MAX_ERASE_TIMEOUT) != HAL_OK) {
        return HAL_ERROR;
    }


    return HAL_OK;
}

static uint8_t QSPI_AutoPollingMemReady(uint32_t Timeout) {

    QSPI_CommandTypeDef sCommand;
    QSPI_AutoPollingTypeDef sConfig;

    /* Configure automatic polling mode to wait for memory ready ------ */
    sCommand.InstructionMode = QSPI_INSTRUCTION_1_LINE;
    sCommand.Instruction = READ_STATUS_REG_CMD;
    sCommand.AddressMode = QSPI_ADDRESS_NONE;
    sCommand.AlternateByteMode = QSPI_ALTERNATE_BYTES_NONE;
    sCommand.DataMode = QSPI_DATA_1_LINE;
    sCommand.DummyCycles = 0;
    sCommand.DdrMode = QSPI_DDR_MODE_DISABLE;
    sCommand.DdrHoldHalfCycle = QSPI_DDR_HHC_ANALOG_DELAY;
    sCommand.SIOOMode = QSPI_SIOO_INST_EVERY_CMD;

    sConfig.Match = 0x0000;
    sConfig.Mask = 0x0101;
    sConfig.MatchMode = QSPI_MATCH_MODE_AND;
    sConfig.StatusBytesSize = 2;
    sConfig.Interval = 0x10;
    sConfig.AutomaticStop = QSPI_AUTOMATIC_STOP_ENABLE;

    if (HAL_QSPI_AutoPolling(&hqspi, &sCommand, &sConfig, Timeout) != HAL_OK) {
        return HAL_ERROR;
    }

    return HAL_OK;
}

static uint8_t QSPI_WriteEnable(void) {
    QSPI_CommandTypeDef sCommand;
    QSPI_AutoPollingTypeDef sConfig;

    /* Enable write operations ------------------------------------------ */
    sCommand.InstructionMode = QSPI_INSTRUCTION_1_LINE;
    sCommand.Instruction = WRITE_ENABLE_CMD;
    sCommand.AddressMode = QSPI_ADDRESS_NONE;
    sCommand.AlternateByteMode = QSPI_ALTERNATE_BYTES_NONE;
    sCommand.DataMode = QSPI_DATA_NONE;
    sCommand.DummyCycles = 0;
    sCommand.DdrMode = QSPI_DDR_MODE_DISABLE;
    sCommand.DdrHoldHalfCycle = QSPI_DDR_HHC_ANALOG_DELAY;
    sCommand.SIOOMode = QSPI_SIOO_INST_EVERY_CMD;

    if (HAL_QSPI_Command(&hqspi, &sCommand, HAL_QPSI_TIMEOUT_DEFAULT_VALUE)
        != HAL_OK) {
        return HAL_ERROR;
    }

    /* Configure automatic polling mode to wait for write enabling ---- */
    sConfig.Match = 0x0202;
    sConfig.Mask = 0x0202;
    sConfig.MatchMode = QSPI_MATCH_MODE_AND;
    sConfig.StatusBytesSize = 2;
    sConfig.Interval = 0x10;
    sConfig.AutomaticStop = QSPI_AUTOMATIC_STOP_ENABLE;

    sCommand.Instruction = READ_STATUS_REG_CMD;
    sCommand.DataMode = QSPI_DATA_1_LINE;
    if (HAL_QSPI_AutoPolling(&hqspi, &sCommand, &sConfig,
                             HAL_QPSI_TIMEOUT_DEFAULT_VALUE) != HAL_OK) {
        return HAL_ERROR;
    }

    return HAL_OK;
}

/*Enable quad mode and set dummy cycles count*/
static uint8_t QSPI_Configuration(void) {

    QSPI_CommandTypeDef sCommand;
    uint16_t reg;


    /*enter 4 byte address*/
    sCommand.InstructionMode = QSPI_INSTRUCTION_1_LINE;
    sCommand.Instruction = ENTER_4_BYTE_ADD_CMD;
    sCommand.AddressMode = QSPI_ADDRESS_NONE;
    sCommand.AlternateByteMode = QSPI_ALTERNATE_BYTES_NONE;
    sCommand.DataMode = QSPI_DATA_NONE;
    sCommand.DummyCycles = 0;
    sCommand.DdrMode = QSPI_DDR_MODE_DISABLE;
    sCommand.DdrHoldHalfCycle = QSPI_DDR_HHC_ANALOG_DELAY;
    sCommand.SIOOMode = QSPI_SIOO_INST_EVERY_CMD;
    sCommand.NbData = 0;

    if (HAL_QSPI_Command(&hqspi, &sCommand, HAL_QPSI_TIMEOUT_DEFAULT_VALUE)
        != HAL_OK) {
        return HAL_ERROR;
    }


    /*read configuration register*/
    sCommand.InstructionMode = QSPI_INSTRUCTION_1_LINE;
    sCommand.Instruction = READ_CONFIGURATION_REG_CMD;
    sCommand.AddressMode = QSPI_ADDRESS_NONE;
    sCommand.AlternateByteMode = QSPI_ALTERNATE_BYTES_NONE;
    sCommand.DataMode = QSPI_DATA_1_LINE;
    sCommand.DummyCycles = 0;
    sCommand.DdrMode = QSPI_DDR_MODE_DISABLE;
    sCommand.DdrHoldHalfCycle = QSPI_DDR_HHC_ANALOG_DELAY;
    sCommand.SIOOMode = QSPI_SIOO_INST_EVERY_CMD;
    sCommand.NbData = 2;

    if (HAL_QSPI_Command(&hqspi, &sCommand, HAL_QPSI_TIMEOUT_DEFAULT_VALUE)
        != HAL_OK) {
        return HAL_ERROR;
    }


    if (HAL_QSPI_Receive(&hqspi, (uint8_t*)(&reg),
                         HAL_QPSI_TIMEOUT_DEFAULT_VALUE) != HAL_OK) {
        return HAL_ERROR;
    }



    if (QSPI_WriteEnable() != HAL_OK) {

        return HAL_ERROR;
    }


    /*set dummy cycles*/
    MODIFY_REG(reg, 0xF0F0, ((DUMMY_CLOCK_CYCLES_READ_QUAD << 4) |
                             (DUMMY_CLOCK_CYCLES_READ_QUAD << 12)));


    sCommand.Instruction = WRITE_VOL_CFG_REG_CMD;


    if (HAL_QSPI_Command(&hqspi, &sCommand, HAL_QPSI_TIMEOUT_DEFAULT_VALUE)
        != HAL_OK) {
        return HAL_ERROR;
    }

    if (HAL_QSPI_Transmit(&hqspi, (uint8_t*)(&reg),
                          HAL_QPSI_TIMEOUT_DEFAULT_VALUE) != HAL_OK) {
        return HAL_ERROR;
    }
    return HAL_OK;
}

uint8_t CSP_QSPI_EraseSector(uint32_t EraseStartAddress, uint32_t EraseEndAddress) {

    QSPI_CommandTypeDef sCommand;

    EraseStartAddress = EraseStartAddress
                        - EraseStartAddress % MEMORY_SECTOR_SIZE;

    /* Erasing Sequence -------------------------------------------------- */
    sCommand.InstructionMode = QSPI_INSTRUCTION_1_LINE;
    sCommand.AddressSize = QSPI_ADDRESS_32_BITS;
    sCommand.AlternateByteMode = QSPI_ALTERNATE_BYTES_NONE;
    sCommand.DdrMode = QSPI_DDR_MODE_DISABLE;
    sCommand.DdrHoldHalfCycle = QSPI_DDR_HHC_ANALOG_DELAY;
    sCommand.SIOOMode = QSPI_SIOO_INST_EVERY_CMD;
    sCommand.Instruction = SECTOR_ERASE_CMD;
    sCommand.AddressMode = QSPI_ADDRESS_1_LINE;

    sCommand.DataMode = QSPI_DATA_NONE;
    sCommand.DummyCycles = 0;

    while (EraseEndAddress >= EraseStartAddress) {
        sCommand.Address = (EraseStartAddress & 0x0FFFFFFF);

        if (QSPI_WriteEnable() != HAL_OK) {
            return HAL_ERROR;
        }

        if (HAL_QSPI_Command(&hqspi, &sCommand, HAL_QPSI_TIMEOUT_DEFAULT_VALUE)
            != HAL_OK) {
            return HAL_ERROR;
        }
        EraseStartAddress += MEMORY_SECTOR_SIZE;

        if (QSPI_AutoPollingMemReady(HAL_QPSI_TIMEOUT_DEFAULT_VALUE) != HAL_OK) {
            return HAL_ERROR;
        }
    }

    return HAL_OK;
}

uint8_t CSP_QSPI_WriteMemory(uint8_t* buffer, uint32_t address, uint32_t buffer_size) {

    QSPI_CommandTypeDef sCommand;
    uint32_t end_addr, current_size, current_addr;

    /* Calculation of the size between the write address and the end of the page */
    current_addr = 0;

    while (current_addr <= address) {
        current_addr += MEMORY_PAGE_SIZE;
    }
    current_size = current_addr - address;

    /* Check if the size of the data is less than the remaining place in the page */
    if (current_size > buffer_size) {
        current_size = buffer_size;
    }

    /* Initialize the adress variables */
    current_addr = address;
    end_addr = address + buffer_size;

    sCommand.InstructionMode = QSPI_INSTRUCTION_1_LINE;
    sCommand.AddressSize = QSPI_ADDRESS_32_BITS;
    sCommand.AlternateByteMode = QSPI_ALTERNATE_BYTES_NONE;
    sCommand.DdrMode = QSPI_DDR_MODE_DISABLE;
    sCommand.DdrHoldHalfCycle = QSPI_DDR_HHC_ANALOG_DELAY;
    sCommand.SIOOMode = QSPI_SIOO_INST_EVERY_CMD;
    sCommand.Instruction = QUAD_IN_FAST_PROG_CMD;
    sCommand.AddressMode = QSPI_ADDRESS_1_LINE;
    sCommand.DataMode = QSPI_DATA_4_LINES;
    sCommand.NbData = buffer_size;
    sCommand.Address = address;
    sCommand.DummyCycles = 0;

    /* Perform the write page by page */
    do {
        sCommand.Address = current_addr;
        sCommand.NbData = current_size;

        if (current_size == 0) {
            return HAL_OK;
        }

        /* Enable write operations */
        if (QSPI_WriteEnable() != HAL_OK) {
            return HAL_ERROR;
        }

        /* Configure the command */
        if (HAL_QSPI_Command(&hqspi, &sCommand, HAL_QPSI_TIMEOUT_DEFAULT_VALUE)
            != HAL_OK) {
            return HAL_ERROR;
        }

        /* Transmission of the data */
        if (HAL_QSPI_Transmit(&hqspi, buffer, HAL_QPSI_TIMEOUT_DEFAULT_VALUE) != HAL_OK) {
            return HAL_ERROR;
        }

        /* Configure automatic polling mode to wait for end of program */
        if (QSPI_AutoPollingMemReady(HAL_QPSI_TIMEOUT_DEFAULT_VALUE) != HAL_OK) {
            return HAL_ERROR;
        }

        /* Update the address and size variables for next page programming */
        current_addr += current_size;
        buffer += current_size;
        current_size =
            ((current_addr + MEMORY_PAGE_SIZE) > end_addr) ?
            (end_addr - current_addr) : MEMORY_PAGE_SIZE;
    } while (current_addr <= end_addr);

    return HAL_OK;

}


uint8_t CSP_QSPI_EnableMemoryMappedMode(void) {

    QSPI_CommandTypeDef sCommand;
    QSPI_MemoryMappedTypeDef sMemMappedCfg;

    /* Enable Memory-Mapped mode-------------------------------------------------- */

    sCommand.InstructionMode = QSPI_INSTRUCTION_1_LINE;
    sCommand.AddressSize = QSPI_ADDRESS_32_BITS;
    sCommand.AlternateByteMode = QSPI_ALTERNATE_BYTES_NONE;
    sCommand.DdrMode = QSPI_DDR_MODE_DISABLE;
    sCommand.DdrHoldHalfCycle = QSPI_DDR_HHC_ANALOG_DELAY;
    sCommand.SIOOMode = QSPI_SIOO_INST_EVERY_CMD;
    sCommand.AddressMode = QSPI_ADDRESS_1_LINE;
    sCommand.DataMode = QSPI_DATA_4_LINES;
    sCommand.NbData = 0;
    sCommand.Address = 0;
    sCommand.Instruction = QUAD_OUT_FAST_READ_CMD;
    sCommand.DummyCycles = DUMMY_CLOCK_CYCLES_READ_QUAD - 2;

    sMemMappedCfg.TimeOutActivation = QSPI_TIMEOUT_COUNTER_DISABLE;

    if (HAL_QSPI_MemoryMapped(&hqspi, &sCommand, &sMemMappedCfg) != HAL_OK) {
        return HAL_ERROR;
    }
    return HAL_OK;
}

static uint8_t QSPI_ResetChip() {
    QSPI_CommandTypeDef sCommand;
    uint32_t temp = 0;
    /* Erasing Sequence -------------------------------------------------- */
    sCommand.InstructionMode = QSPI_INSTRUCTION_1_LINE;
    sCommand.AddressSize = QSPI_ADDRESS_32_BITS;
    sCommand.AlternateByteMode = QSPI_ALTERNATE_BYTES_NONE;
    sCommand.DdrMode = QSPI_DDR_MODE_DISABLE;
    sCommand.DdrHoldHalfCycle = QSPI_DDR_HHC_ANALOG_DELAY;
    sCommand.SIOOMode = QSPI_SIOO_INST_EVERY_CMD;
    sCommand.Instruction = RESET_ENABLE_CMD;
    sCommand.AddressMode = QSPI_ADDRESS_NONE;
    sCommand.Address = 0;
    sCommand.DataMode = QSPI_DATA_NONE;
    sCommand.DummyCycles = 0;

    if (HAL_QSPI_Command(&hqspi, &sCommand, HAL_QPSI_TIMEOUT_DEFAULT_VALUE)
        != HAL_OK) {
        return HAL_ERROR;
    }
    for (temp = 0; temp < 0x2f; temp++) {
        __NOP();
    }

    sCommand.InstructionMode = QSPI_INSTRUCTION_1_LINE;
    sCommand.AddressSize = QSPI_ADDRESS_32_BITS;
    sCommand.AlternateByteMode = QSPI_ALTERNATE_BYTES_NONE;
    sCommand.DdrMode = QSPI_DDR_MODE_DISABLE;
    sCommand.DdrHoldHalfCycle = QSPI_DDR_HHC_ANALOG_DELAY;
    sCommand.SIOOMode = QSPI_SIOO_INST_EVERY_CMD;
    sCommand.Instruction = RESET_EXECUTE_CMD;
    sCommand.AddressMode = QSPI_ADDRESS_NONE;
    sCommand.Address = 0;
    sCommand.DataMode = QSPI_DATA_NONE;
    sCommand.DummyCycles = 0;

    if (HAL_QSPI_Command(&hqspi, &sCommand, HAL_QPSI_TIMEOUT_DEFAULT_VALUE)
        != HAL_OK) {
        return HAL_ERROR;
    }

#if 0
    /* Erasing Sequence -------------------------------------------------- */
    sCommand.InstructionMode = QSPI_INSTRUCTION_2_LINES;
    sCommand.AddressSize = QSPI_ADDRESS_32_BITS;
    sCommand.AlternateByteMode = QSPI_ALTERNATE_BYTES_NONE;
    sCommand.DdrMode = QSPI_DDR_MODE_DISABLE;
    sCommand.DdrHoldHalfCycle = QSPI_DDR_HHC_ANALOG_DELAY;
    sCommand.SIOOMode = QSPI_SIOO_INST_EVERY_CMD;
    sCommand.Instruction = RESET_ENABLE_CMD;
    sCommand.AddressMode = QSPI_ADDRESS_NONE;
    sCommand.Address = 0;
    sCommand.DataMode = QSPI_DATA_NONE;
    sCommand.DummyCycles = 0;

    if (HAL_QSPI_Command(&hqspi, &sCommand, HAL_QPSI_TIMEOUT_DEFAULT_VALUE)
        != HAL_OK) {
        return HAL_ERROR;
    }
    for (temp = 0; temp < 0x2f; temp++) {
        __NOP();
    }

    sCommand.InstructionMode = QSPI_INSTRUCTION_2_LINES;
    sCommand.AddressSize = QSPI_ADDRESS_32_BITS;
    sCommand.AlternateByteMode = QSPI_ALTERNATE_BYTES_NONE;
    sCommand.DdrMode = QSPI_DDR_MODE_DISABLE;
    sCommand.DdrHoldHalfCycle = QSPI_DDR_HHC_ANALOG_DELAY;
    sCommand.SIOOMode = QSPI_SIOO_INST_EVERY_CMD;
    sCommand.Instruction = RESET_EXECUTE_CMD;
    sCommand.AddressMode = QSPI_ADDRESS_NONE;
    sCommand.Address = 0;
    sCommand.DataMode = QSPI_DATA_NONE;
    sCommand.DummyCycles = 0;

    if (HAL_QSPI_Command(&hqspi, &sCommand, HAL_QPSI_TIMEOUT_DEFAULT_VALUE)
        != HAL_OK) {
        return HAL_ERROR;
    }

    /* Erasing Sequence -------------------------------------------------- */
    sCommand.InstructionMode = QSPI_INSTRUCTION_4_LINES;
    sCommand.AddressSize = QSPI_ADDRESS_32_BITS;
    sCommand.AlternateByteMode = QSPI_ALTERNATE_BYTES_NONE;
    sCommand.DdrMode = QSPI_DDR_MODE_DISABLE;
    sCommand.DdrHoldHalfCycle = QSPI_DDR_HHC_ANALOG_DELAY;
    sCommand.SIOOMode = QSPI_SIOO_INST_EVERY_CMD;
    sCommand.Instruction = RESET_ENABLE_CMD;
    sCommand.AddressMode = QSPI_ADDRESS_NONE;
    sCommand.Address = 0;
    sCommand.DataMode = QSPI_DATA_NONE;
    sCommand.DummyCycles = 0;

    if (HAL_QSPI_Command(&hqspi, &sCommand, HAL_QPSI_TIMEOUT_DEFAULT_VALUE)
        != HAL_OK) {
        return HAL_ERROR;
    }
    for (temp = 0; temp < 0x2f; temp++) {
        __NOP();
    }

    sCommand.InstructionMode = QSPI_INSTRUCTION_4_LINES;
    sCommand.AddressSize = QSPI_ADDRESS_32_BITS;
    sCommand.AlternateByteMode = QSPI_ALTERNATE_BYTES_NONE;
    sCommand.DdrMode = QSPI_DDR_MODE_DISABLE;
    sCommand.DdrHoldHalfCycle = QSPI_DDR_HHC_ANALOG_DELAY;
    sCommand.SIOOMode = QSPI_SIOO_INST_EVERY_CMD;
    sCommand.Instruction = RESET_EXECUTE_CMD;
    sCommand.AddressMode = QSPI_ADDRESS_NONE;
    sCommand.Address = 0;
    sCommand.DataMode = QSPI_DATA_NONE;
    sCommand.DummyCycles = 0;

    if (HAL_QSPI_Command(&hqspi, &sCommand, HAL_QPSI_TIMEOUT_DEFAULT_VALUE)
        != HAL_OK) {
        return HAL_ERROR;
    }
#endif

    return HAL_OK;
}
/* USER CODE END 1 */

/************************ (C) COPYRIGHT STMicroelectronics *****END OF FILE****/
