akkdong/FlightComputer/src/FlightComputer/Common/Src/lwrb.c

/**
 * \file            lwrb.c
 * \brief           Lightweight ring buffer
 */

/*
 * Copyright (c) 2020 Tilen MAJERLE
 *
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
 * This file is part of LwRB - Lightweight ring buffer library.
 *
 * Author:          Tilen MAJERLE <tilen@majerle.eu>
 * Version:         v2.0.3
 */
#include "lwrb/lwrb.h"

/* Memory set and copy functions */
#define BUF_MEMSET                      memset
#define BUF_MEMCPY                      memcpy

#define BUF_MAGIC1                      (0xDEADBEEF)
#define BUF_MAGIC2                      (~0xDEADBEEF)

#if LWRB_USE_MAGIC
#define BUF_IS_VALID(b)                 ((b) != NULL && (b)->magic1 == BUF_MAGIC1 && (b)->magic2 == BUF_MAGIC2 && (b)->buff != NULL && (b)->size > 0)
#else
#define BUF_IS_VALID(b)                 ((b) != NULL && (b)->buff != NULL && (b)->size > 0)
#endif /* LWRB_USE_MAGIC */
#define BUF_MIN(x, y)                   ((x) < (y) ? (x) : (y))
#define BUF_MAX(x, y)                   ((x) > (y) ? (x) : (y))
#define BUF_SEND_EVT(b, type, bp)       do { if ((b)->evt_fn != NULL) { (b)->evt_fn((b), (type), (bp)); } } while (0)

/**
 * \brief           Initialize buffer handle to default values with size and buffer data array
 * \param[in]       buff: Buffer handle
 * \param[in]       buffdata: Pointer to memory to use as buffer data
 * \param[in]       size: Size of `buffdata` in units of bytes
 *                      Maximum number of bytes buffer can hold is `size - 1`
 * \return          `1` on success, `0` otherwise
 */
uint8_t
lwrb_init(lwrb_t* buff, void* buffdata, size_t size) {
    if (buff == NULL || buffdata == NULL || size == 0) {
        return 0;
    }

    BUF_MEMSET((void*)buff, 0x00, sizeof(*buff));

    buff->size = size;
    buff->buff = buffdata;

#if LWRB_USE_MAGIC
    buff->magic1 = BUF_MAGIC1;
    buff->magic2 = BUF_MAGIC2;
#endif /* LWRB_USE_MAGIC */

    return 1;
}

/**
 * \brief           Check if buff is initialized and ready to use
 * \param[in]       buff: Buffer handle
 * \return          `1` if ready, `0` otherwise
 */
uint8_t
lwrb_is_ready(lwrb_t* buff) {
    return BUF_IS_VALID(buff);
}

/**
 * \brief           Free buffer memory
 * \note            Since implementation does not use dynamic allocation,
 *                  it just sets buffer handle to `NULL`
 * \param[in]       buff: Buffer handle
 */
void
lwrb_free(lwrb_t* buff) {
    if (BUF_IS_VALID(buff)) {
        buff->buff = NULL;
    }
}

/**
 * \brief           Set event function callback for different buffer operations
 * \param[in]       buff: Buffer handle
 * \param[in]       evt_fn: Callback function
 */
void
lwrb_set_evt_fn(lwrb_t* buff, lwrb_evt_fn evt_fn) {
    if (BUF_IS_VALID(buff)) {
        buff->evt_fn = evt_fn;
    }
}

/**
 * \brief           Write data to buffer.
 * Copies data from `data` array to buffer and marks buffer as full for maximum `btw` number of bytes
 *
 * \param[in]       buff: Buffer handle
 * \param[in]       data: Pointer to data to write into buffer
 * \param[in]       btw: Number of bytes to write
 * \return          Number of bytes written to buffer.
 *                      When returned value is less than `btw`, there was no enough memory available
 *                      to copy full data array
 */
size_t
lwrb_write(lwrb_t* buff, const void* data, size_t btw) {
    size_t tocopy, free;
    volatile size_t buff_w_ptr;
    const uint8_t* d = data;

    if (!BUF_IS_VALID(buff) || data == NULL || btw == 0) {
        return 0;
    }

    /* Calculate maximum number of bytes available to write */
    free = lwrb_get_free(buff);
    btw = BUF_MIN(free, btw);
    if (btw == 0) {
        return 0;
    }

    /* Step 1: Write data to linear part of buffer */
    buff_w_ptr = buff->w;
    tocopy = BUF_MIN(buff->size - buff_w_ptr, btw);
    BUF_MEMCPY(&buff->buff[buff_w_ptr], d, tocopy);
    buff_w_ptr += tocopy;
    btw -= tocopy;

    /* Step 2: Write data to beginning of buffer (overflow part) */
    if (btw > 0) {
        BUF_MEMCPY(buff->buff, &d[tocopy], btw);
        buff_w_ptr = btw;
    }

    /* Step 3: Check end of buffer */
    if (buff_w_ptr >= buff->size) {
        buff_w_ptr = 0;
    }

    /*
     * Write final value to the actual running variable.
     * This is to ensure no read operation can access intermediate data
     */
    buff->w = buff_w_ptr;
    
    BUF_SEND_EVT(buff, LWRB_EVT_WRITE, tocopy + btw);
    return tocopy + btw;
}

/**
 * \brief           Write string to buffer.
 * Copies data from `string: null terminated array` to buffer
 *
 * \param[in]       buff: Buffer handle
 * \param[in]       str: Pointer to string to write into buffer
 * \return          Number of bytes written to buffer.
 *                      When returned value is less than `btw`, there was no enough memory available
 *                      to copy full data array
 */
size_t
lwrb_write_string(lwrb_t* buff, const char* str) {
	int len = strlen(str);
	return lwrb_write(buff, str, len);
}

/**
 * \brief           Read data from buffer.
 * Copies data from buffer to `data` array and marks buffer as free for maximum `btr` number of bytes
 *
 * \param[in]       buff: Buffer handle
 * \param[out]      data: Pointer to output memory to copy buffer data to
 * \param[in]       btr: Number of bytes to read
 * \return          Number of bytes read and copied to data array
 */
size_t
lwrb_read(lwrb_t* buff, void* data, size_t btr) {
    size_t tocopy, full;
    volatile size_t buff_r_ptr;
    uint8_t* d = data;

    if (!BUF_IS_VALID(buff) || data == NULL || btr == 0) {
        return 0;
    }

    /* Calculate maximum number of bytes available to read */
    full = lwrb_get_full(buff);
    btr = BUF_MIN(full, btr);
    if (btr == 0) {
        return 0;
    }

    /* Step 1: Read data from linear part of buffer */
    buff_r_ptr = buff->r;
    tocopy = BUF_MIN(buff->size - buff_r_ptr, btr);
    BUF_MEMCPY(d, &buff->buff[buff_r_ptr], tocopy);
    buff_r_ptr += tocopy;
    btr -= tocopy;

    /* Step 2: Read data from beginning of buffer (overflow part) */
    if (btr > 0) {
        BUF_MEMCPY(&d[tocopy], buff->buff, btr);
        buff_r_ptr = btr;
    }

    /* Step 3: Check end of buffer */
    if (buff_r_ptr >= buff->size) {
        buff_r_ptr = 0;
    }

    /*
     * Write final value to the actual running variable.
     * This is to ensure no write operation can access intermediate data
     */
    buff->r = buff_r_ptr;

    BUF_SEND_EVT(buff, LWRB_EVT_READ, tocopy + btr);
    return tocopy + btr;
}

/**
 * \brief           Read from buffer without changing read pointer (peek only)
 * \param[in]       buff: Buffer handle
 * \param[in]       skip_count: Number of bytes to skip before reading data
 * \param[out]      data: Pointer to output memory to copy buffer data to
 * \param[in]       btp: Number of bytes to peek
 * \return          Number of bytes peeked and written to output array
 */
size_t
lwrb_peek(lwrb_t* buff, size_t skip_count, void* data, size_t btp) {
    size_t full, tocopy;
    volatile size_t r;
    uint8_t* d = data;

    if (!BUF_IS_VALID(buff) || data == NULL || btp == 0) {
        return 0;
    }

    r = buff->r;

    /* Calculate maximum number of bytes available to read */
    full = lwrb_get_full(buff);

    /* Skip beginning of buffer */
    if (skip_count >= full) {
        return 0;
    }
    r += skip_count;
    full -= skip_count;
    if (r >= buff->size) {
        r -= buff->size;
    }

    /* Check maximum number of bytes available to read after skip */
    btp = BUF_MIN(full, btp);
    if (btp == 0) {
        return 0;
    }

    /* Step 1: Read data from linear part of buffer */
    tocopy = BUF_MIN(buff->size - r, btp);
    BUF_MEMCPY(d, &buff->buff[r], tocopy);
    btp -= tocopy;

    /* Step 2: Read data from beginning of buffer (overflow part) */
    if (btp > 0) {
        BUF_MEMCPY(&d[tocopy], buff->buff, btp);
    }
    return tocopy + btp;
}

/**
 * \brief           Get available size in buffer for write operation
 * \param[in]       buff: Buffer handle
 * \return          Number of free bytes in memory
 */
size_t
lwrb_get_free(lwrb_t* buff) {
    size_t size;
    volatile size_t w, r;

    if (!BUF_IS_VALID(buff)) {
        return 0;
    }

    /* Use temporary values in case they are changed during operations */
    w = buff->w;
    r = buff->r;
    if (w == r) {
        size = buff->size;
    } else if (r > w) {
        size = r - w;
    } else {
        size = buff->size - (w - r);
    }

    /* Buffer free size is always 1 less than actual size */
    return size - 1;
}

/**
 * \brief           Get number of bytes currently available in buffer
 * \param[in]       buff: Buffer handle
 * \return          Number of bytes ready to be read
 */
size_t
lwrb_get_full(lwrb_t* buff) {
    size_t size;
    volatile size_t w, r;

    if (!BUF_IS_VALID(buff)) {
        return 0;
    }

    /* Use temporary values in case they are changed during operations */
    w = buff->w;
    r = buff->r;
    if (w == r) {
        size = 0;
    } else if (w > r) {
        size = w - r;
    } else {
        size = buff->size - (r - w);
    }
    return size;
}

/**
 * \brief           Resets buffer to default values. Buffer size is not modified
 * \note            This function is not thread safe.
 *                      When used, application must ensure there is no active read/write operation
 * \param[in]       buff: Buffer handle
 */
void
lwrb_reset(lwrb_t* buff) {
    if (BUF_IS_VALID(buff)) {
        buff->w = 0;
        buff->r = 0;
        BUF_SEND_EVT(buff, LWRB_EVT_RESET, 0);
    }
}

/**
 * \brief           Get linear address for buffer for fast read
 * \param[in]       buff: Buffer handle
 * \return          Linear buffer start address
 */
void*
lwrb_get_linear_block_read_address(lwrb_t* buff) {
    if (!BUF_IS_VALID(buff)) {
        return NULL;
    }
    return &buff->buff[buff->r];
}

/**
 * \brief           Get length of linear block address before it overflows for read operation
 * \param[in]       buff: Buffer handle
 * \return          Linear buffer size in units of bytes for read operation
 */
size_t
lwrb_get_linear_block_read_length(lwrb_t* buff) {
    size_t len;
    volatile size_t w, r;

    if (!BUF_IS_VALID(buff)) {
        return 0;
    }

    /* Use temporary values in case they are changed during operations */
    w = buff->w;
    r = buff->r;
    if (w > r) {
        len = w - r;
    } else if (r > w) {
        len = buff->size - r;
    } else {
        len = 0;
    }
    return len;
}

/**
 * \brief           Skip (ignore; advance read pointer) buffer data
 * Marks data as read in the buffer and increases free memory for up to `len` bytes
 *
 * \note            Useful at the end of streaming transfer such as DMA
 * \param[in]       buff: Buffer handle
 * \param[in]       len: Number of bytes to skip and mark as read
 * \return          Number of bytes skipped
 */
size_t
lwrb_skip(lwrb_t* buff, size_t len) {
    size_t full;
    volatile size_t r;

    if (!BUF_IS_VALID(buff) || len == 0) {
        return 0;
    }

    full = lwrb_get_full(buff);
    len = BUF_MIN(len, full);
    r = buff->r + len;
    if (r >= buff->size) {
        r -= buff->size;
    }
    buff->r = r;
    BUF_SEND_EVT(buff, LWRB_EVT_READ, len);
    return len;
}

/**
 * \brief           Get linear address for buffer for fast read
 * \param[in]       buff: Buffer handle
 * \return          Linear buffer start address
 */
void*
lwrb_get_linear_block_write_address(lwrb_t* buff) {
    if (!BUF_IS_VALID(buff)) {
        return NULL;
    }
    return &buff->buff[buff->w];
}

/**
 * \brief           Get length of linear block address before it overflows for write operation
 * \param[in]       buff: Buffer handle
 * \return          Linear buffer size in units of bytes for write operation
 */
size_t
lwrb_get_linear_block_write_length(lwrb_t* buff) {
    size_t len;
    volatile size_t w, r;

    if (!BUF_IS_VALID(buff)) {
        return 0;
    }

    /* Use temporary values in case they are changed during operations */
    w = buff->w;
    r = buff->r;
    if (w >= r) {
        len = buff->size - w;
        /*
         * When read pointer is 0,
         * maximal length is one less as if too many bytes
         * are written, buffer would be considered empty again (r == w)
         */
        if (r == 0) {
            /*
             * Cannot overflow:
             * - If r is not 0, statement does not get called
             * - buff->size cannot be 0 and if r is 0, len is greater 0
             */
            --len;
        }
    } else {
        len = r - w - 1;
    }
    return len;
}

/**
 * \brief           Advance write pointer in the buffer.
 * Similar to skip function but modifies write pointer instead of read
 *
 * \note            Useful when hardware is writing to buffer and application needs to increase number
 *                      of bytes written to buffer by hardware
 * \param[in]       buff: Buffer handle
 * \param[in]       len: Number of bytes to advance
 * \return          Number of bytes advanced for write operation
 */
size_t
lwrb_advance(lwrb_t* buff, size_t len) {
    size_t free;
    volatile size_t w;

    if (!BUF_IS_VALID(buff) || len == 0) {
        return 0;
    }

    /* Use local variables before writing back to main structure */
    free = lwrb_get_free(buff);
    len = BUF_MIN(len, free);
    w = buff->w + len;
    if (w >= buff->size) {
        w -= buff->size;
    }
    buff->w = w;
    BUF_SEND_EVT(buff, LWRB_EVT_WRITE, len);
    return len;
}
