akkdong/FlightComputer/src/ExternalLoader/CM7/Core/Src/Dev_Inf.c

// Dev_Inf.c
//

#include "main.h"
#include "Dev_Inf.h"
#include "quadspi.h"


/* This structure containes information used by ST-LINK Utility to program and erase the device */
#if defined (__ICCARM__)
__root struct StorageInfo const StorageInfo  =  {
#else
struct StorageInfo const StorageInfo  =  {
#endif
	"FCExternalLoader_STM32H745", 	 	// Device Name + EVAL Borad name
	SPI_FLASH,                   		// Device Type
	0x90000000,                			// Device Start Address
	MEMORY_FLASH_SIZE,                  // Device Size in Bytes
	MEMORY_PAGE_SIZE,                   // Programming Page Size
	0xFF,                       		// Initial Content of Erased Memory
	// Specify Size and Address of Sectors (view example below)
	{
		{
			(MEMORY_FLASH_SIZE / MEMORY_SECTOR_SIZE),  // Sector Numbers,
			(uint32_t) MEMORY_SECTOR_SIZE
		},
		{
			0x00000000,
			0x00000000
		}
	}
};
