akkdong/FlightComputer/src/FlightComputer/CM7/Core/Inc/UART_Conf.h

// UART_Conf.h
//

#ifndef __UART_CONF_H__
#define __UART_CONF_H__

#ifndef MAX_RX_BUFFER
#define	MAX_RX_BUFFER			(64)
#endif

#ifndef MAX_TX_BUFFER
#define MAX_TX_BUFFER			(64)
#endif

#define SUPPORT_UART1			(1)
#define SUPPORT_UART2			(1)
#define SUPPORT_UART3			(1)
#define SUPPORT_UART4			(0)
#define SUPPORT_UART5			(0)
#define SUPPORT_UART6			(0)
#define SUPPORT_UART7			(0)
#define SUPPORT_UART8			(0)



#endif // __UART_CONF_H__
