akkdong/FlightComputer/src/FlightComputer/Common/Inc/RingBuffer.h

// RingBuffer.h
//

#ifndef __RINGBUFFER_H__
#define __RINGBUFFER_H__


////////////////////////////////////////////////////////////////////////////////////////////////
//

typedef struct _RingBuffer
{
	uint8_t*	data;
	uint16_t	size;

	uint16_t	head;
	uint16_t	tail;

} RingBuffer;


////////////////////////////////////////////////////////////////////////////////////////////////
//

void    RB_Init(RingBuffer* rb, uint8_t * data, uint16_t size);

int32_t	RB_GetBufferCount(RingBuffer* rb);
int32_t	RB_GetDataCount(RingBuffer* rb);

int32_t	RB_IsFull(RingBuffer* rb);
int32_t	RB_IsEmpty(RingBuffer* rb);

int32_t	RB_Push(RingBuffer* rb, uint8_t data);
int32_t	RB_PushBack(RingBuffer* rb, uint8_t data);
int32_t	RB_Pop(RingBuffer* rb);
int32_t	RB_Peek(RingBuffer* rb);

void	RB_Empty(RingBuffer* rb);


#endif // __RINGBUFFER_H__
