akkdong/FlightComputer/src/Test/ExtraCoreTest/CM7/Core/Src/main.c

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
/* Includes ------------------------------------------------------------------*/
#include "main.h"

/* USER CODE BEGIN Includes */
#include <stdio.h>
#include <string.h>

#include "sdram.h"
#include "quadspi.h"
#include "nor.h"
#include "beep.h"
#include "serial.h"
#include "shell.h"

#include "lwshell/lwshell.h"
/* USER CODE END Includes */

/* USER CODE BEGIN PD */

#ifndef HSEM_ID_0
#define HSEM_ID_0 (0U) /* HW semaphore 0*/
#endif

#ifndef HSEM_ID_1
#define HSEM_ID_1 (1U) /* HW semaphore 1*/
#endif

/* USER CODE END PD */

/* USER CODE BEGIN PM */

#define ENABLE_QSPI_TEST				(1)
#define ENABLE_SDRAM_TEST				(1)
#define ENABLE_NOR_TEST					(1)

#define PWR_WAKEUP_FLAGS  (PWR_WAKEUP_FLAG1 | PWR_WAKEUP_FLAG2 | PWR_WAKEUP_FLAG3 | \
                           PWR_WAKEUP_FLAG4 | PWR_WAKEUP_FLAG5 | PWR_WAKEUP_FLAG6)

/* USER CODE END PM */


DMA2D_HandleTypeDef hdma2d;

I2C_HandleTypeDef hi2c1;

UART_HandleTypeDef hlpuart1;

LTDC_HandleTypeDef hltdc;

QSPI_HandleTypeDef hqspi;

RTC_HandleTypeDef hrtc;

TIM_HandleTypeDef htim3;
TIM_HandleTypeDef htim4;
DMA_HandleTypeDef hdma_tim4_ch1;
DMA_HandleTypeDef hdma_tim4_ch2;

NOR_HandleTypeDef hnor1;
SDRAM_HandleTypeDef hsdram1;

void SystemClock_Config(void);
void PeriphCommonClock_Config(void);
static void MX_GPIO_Init(void);
static void MX_DMA_Init(void);
static void MX_FMC_Init(void);
static void MX_QUADSPI_Init(void);
static void MX_LPUART1_UART_Init(void);
static void MX_I2C1_Init(void);
static void MX_LTDC_Init(void);
static void MX_TIM3_Init(void);
static void MX_TIM4_Init(void);
static void MX_RTC_Init(void);
static void MX_DMA2D_Init(void);
/* USER CODE BEGIN PFP */
static void MPU_Config(void);
/* USER CODE END PFP */

/* USER CODE BEGIN 0 */
//int __io_putchar(int ch)
//{
//	//HAL_UART_Transmit(&hlpuart1, (uint8_t *)&ch, 1, 100);
//	serial_write(ch);
//	return 1;
//}
int _write(int file, char *ptr, int len)
{
	for (int i = 0; i < len; i++)
		serial_write(ptr[i]);

	return len;
}
/* USER CODE END 0 */

/**
  * @brief  The application entry point.
  * @retval int
  */
int main(void)
{
  /* USER CODE BEGIN 1 */
#if ENABLE_NOR_TEST || 1
	MPU_Config();
#endif
  /* USER CODE END 1 */
/* USER CODE BEGIN Boot_Mode_Sequence_0 */
  int32_t timeout;
/* USER CODE END Boot_Mode_Sequence_0 */

  /* Enable I-Cache---------------------------------------------------------*/
  SCB_EnableICache();

  /* Enable D-Cache---------------------------------------------------------*/
  SCB_EnableDCache();

/* USER CODE BEGIN Boot_Mode_Sequence_1 */
  /* Wait until CPU2 boots and enters in stop mode or timeout*/
  timeout = 0xFFFF;
  while((__HAL_RCC_GET_FLAG(RCC_FLAG_D2CKRDY) != RESET) && (timeout-- > 0));
  if ( timeout < 0 )
  {
	  Error_Handler();
  }
/* USER CODE END Boot_Mode_Sequence_1 */
  /* MCU Configuration--------------------------------------------------------*/

  /* Reset of all peripherals, Initializes the Flash interface and the Systick. */
  HAL_Init();

  /* Configure the system clock */
  SystemClock_Config();

	/* Configure the peripherals common clocks */
	  PeriphCommonClock_Config();
	/* USER CODE BEGIN Boot_Mode_Sequence_2 */
	/* When system initialization is finished, Cortex-M7 will release Cortex-M4 by means of
	HSEM notification */
	/*HW semaphore Clock enable*/
	__HAL_RCC_HSEM_CLK_ENABLE();
	/*Take HSEM */
	HAL_HSEM_FastTake(HSEM_ID_0);
	/*Release HSEM in order to notify the CPU2(CM4)*/
	HAL_HSEM_Release(HSEM_ID_0,0);
	/* wait until CPU2 wakes up from stop mode */
	timeout = 0xFFFF;
	while((__HAL_RCC_GET_FLAG(RCC_FLAG_D2CKRDY) == RESET) && (timeout-- > 0));
	if ( timeout < 0 )
	{
		Error_Handler();
	}
	/* USER CODE END Boot_Mode_Sequence_2 */

  /* USER CODE BEGIN SysInit */

	/* Check and handle if the system was resumed from StandBy mode */
	if(__HAL_PWR_GET_FLAG(PWR_FLAG_SB) != RESET)
	{
	  /* Clear system Standby flag */
	  __HAL_PWR_CLEAR_FLAG(PWR_FLAG_SB);
	}

  /* USER CODE END SysInit */

  /* Initialize all configured peripherals */
  MX_GPIO_Init();
  MX_DMA_Init();
  MX_FMC_Init();
  MX_QUADSPI_Init();
  MX_LPUART1_UART_Init();
  MX_I2C1_Init();
  MX_LTDC_Init();
  MX_TIM3_Init();
  MX_TIM4_Init();
  MX_RTC_Init();
  MX_DMA2D_Init();
  /* USER CODE BEGIN 2 */

  serial_init(&hlpuart1);

#if 0
  /* The Following Wakeup sequence is highly recommended prior to each Standby mode entry
    mainly  when using more than one wakeup source this is to not miss any wakeup event.
    - Disable all used wakeup sources,
    - Clear all related wakeup flags,
    - Re-enable all used wakeup sources,
    - Enter the Standby mode.
  */
  /* Disable all used wakeup sources*/
  HAL_PWREx_DisableWakeUpPin(PWR_WAKEUP_PIN4);

  /* Re-enable all used wakeup sources*/
  /* Configure Wakeup pin */
  PWREx_WakeupPinTypeDef sPinParams;
  sPinParams.WakeUpPin    = PWR_WAKEUP_PIN4;
  sPinParams.PinPolarity  = PWR_PIN_POLARITY_LOW;
  sPinParams.PinPull      = PWR_PIN_NO_PULL;
  HAL_PWREx_EnableWakeUpPin(&sPinParams);

  /* Clear all related wakeup flags */
  HAL_StatusTypeDef ret = HAL_PWREx_ClearWakeupFlag(PWR_WAKEUP_FLAGS);
  if(ret != HAL_OK)
  {
    Error_Handler();
  }
#endif

  /* USER CODE END 2 */

  /* Infinite loop */
  /* USER CODE BEGIN WHILE */

  //
  uint32_t count = 0;
  while (count++ < 10)
  {
	  HAL_GPIO_TogglePin(LED1_GPIO_Port, LED1_Pin);
	  HAL_Delay(100);
  }
  // turn-off
  HAL_GPIO_WritePin(LED1_GPIO_Port, LED1_Pin, GPIO_PIN_SET);
  printf("STM32H745 CoreBoard....\r\n");

  beep_init();
  shell_init();

#if DEPRECATED || 1
  uint32_t tone[] = { 240, 320, 470, 0, 600, 0 };
  uint32_t delay[] = { 200, 200, 200, 100, 400, 100 };
#if 0
  uint32_t tick = HAL_GetTick();
  int i = 0;
  beep_setFreq(tone[i]);
#else
  for (int i = 0; i < sizeof(tone) / sizeof(tone[0]); i++)
  {
	  beep_setFreq(tone[i]);
	  HAL_Delay(delay[i]);
  }
#endif
#endif

  uint32_t blinkTick = HAL_GetTick();
  int blinkType = 0;

  HAL_GPIO_WritePin(LCD_BL_GPIO_Port, LCD_BL_Pin, GPIO_PIN_SET);

  //
  volatile unsigned char* lcd = (volatile unsigned char *)(0xD0000000);
  for (int i = 0; i < 800 * 480 / 3; i++ )
  {
	  *lcd++ = 0xF8;
	  *lcd++ = 0x00;
  }
  for (int i = 0; i < 800 * 480 / 3; i++ )
  {
	  *lcd++ = 0x07;
	  *lcd++ = 0xE0;
  }
  for (int i = 0; i < 800 * 480 / 3; i++ )
  {
	  *lcd++ = 0x00;
	  *lcd++ = 0x1F;
  }


  while (1)
  {
	  shell_process();

#if DEPRECATED || 0
	  if (HAL_GetTick() - tick > delay[i])
	  {
		  tick = HAL_GetTick();

		  i = (i + 1) % (sizeof(delay) / sizeof(delay[0]));
		  if (tone[i])
			  beep_setFreq(tone[i]);
		  else
			  beep_mute();
		  //printf("beep %d Hz   %ld\r\n", (int)tone[i], tick);
	  }
#endif
    /* USER CODE END WHILE */

    /* USER CODE BEGIN 3 */
	  uint32_t blinkDelay = (blinkType == 0) ? 800 : 200;
	  if (HAL_GetTick() - blinkTick > blinkDelay)
	  {
		  blinkTick = HAL_GetTick();
		  HAL_GPIO_TogglePin(LED1_GPIO_Port, LED1_Pin);
		  blinkType = (1 - blinkType);
	  }
  }
  /* USER CODE END 3 */
}

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
/* USER CODE BEGIN 4 */

static void MPU_Config(void)
{
  MPU_Region_InitTypeDef MPU_InitStruct;

  /* Disable the MPU */
  HAL_MPU_Disable();

  /* Configure the MPU attributes as WT for SDRAM */
  MPU_InitStruct.Enable = MPU_REGION_ENABLE;
  MPU_InitStruct.BaseAddress = SDRAM_DEVICE_ADDR;
  MPU_InitStruct.Size = MPU_REGION_SIZE_32MB;
  MPU_InitStruct.AccessPermission = MPU_REGION_FULL_ACCESS;
  MPU_InitStruct.IsBufferable = MPU_ACCESS_NOT_BUFFERABLE;
  MPU_InitStruct.IsCacheable = MPU_ACCESS_CACHEABLE;
  MPU_InitStruct.IsShareable = MPU_ACCESS_NOT_SHAREABLE;
  MPU_InitStruct.Number = MPU_REGION_NUMBER0;
  MPU_InitStruct.TypeExtField = MPU_TEX_LEVEL0;
  MPU_InitStruct.SubRegionDisable = 0x00;
  MPU_InitStruct.DisableExec = MPU_INSTRUCTION_ACCESS_ENABLE;

  HAL_MPU_ConfigRegion(&MPU_InitStruct);

  /* Configure the MPU attributes as WT for NOR */
  MPU_InitStruct.Enable = MPU_REGION_ENABLE;
  MPU_InitStruct.BaseAddress = NOR_DEVICE_ADDR;
  MPU_InitStruct.Size = MPU_REGION_SIZE_16MB;
  MPU_InitStruct.AccessPermission = MPU_REGION_FULL_ACCESS;
  MPU_InitStruct.IsBufferable = MPU_ACCESS_NOT_BUFFERABLE;
  MPU_InitStruct.IsCacheable = MPU_ACCESS_CACHEABLE;
  MPU_InitStruct.IsShareable = MPU_ACCESS_NOT_SHAREABLE;
  MPU_InitStruct.Number = MPU_REGION_NUMBER1;
  MPU_InitStruct.TypeExtField = MPU_TEX_LEVEL0;
  MPU_InitStruct.SubRegionDisable = 0x00;
  MPU_InitStruct.DisableExec = MPU_INSTRUCTION_ACCESS_ENABLE;

  HAL_MPU_ConfigRegion(&MPU_InitStruct);

  /* Enable the MPU */
  HAL_MPU_Enable(MPU_PRIVILEGED_DEFAULT);
}

/* USER CODE END 4 */
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
