akkdong/FlightComputer/src/Test/GY91-Test/Core/Src/main.c

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
/* Includes ------------------------------------------------------------------*/
#include "main.h"

/* USER CODE BEGIN Includes */
#include <stdio.h>
#include "Pressure.h"
/* USER CODE END Includes */

/* USER CODE BEGIN PM */
#define NS       128
#define TIM3CLK  48000000
#define F_SIGNAL 2000
/* USER CODE END PM */

I2C_HandleTypeDef hi2c1;

SPI_HandleTypeDef hspi1;

TIM_HandleTypeDef htim2;
TIM_HandleTypeDef htim3;
TIM_HandleTypeDef htim6;
DMA_HandleTypeDef hdma_tim2_ch1;
DMA_HandleTypeDef hdma_tim3_ch3;
DMA_HandleTypeDef hdma_tim6_up;

UART_HandleTypeDef huart2;

/* USER CODE BEGIN PV */
uint32_t Wave_LUT[NS] = {
    512, 537, 562, 587, 612, 637, 661, 685, 709, 732, 754, 776, 798, 818, 838,
    857, 875, 893, 909, 925, 939, 952, 965, 976, 986, 995, 1002, 1009, 1014, 1018,
    1021, 1023, 1023, 1022, 1020, 1016, 1012, 1006, 999, 990, 981, 970, 959, 946, 932,
    917, 901, 884, 866, 848, 828, 808, 787, 765, 743, 720, 697, 673, 649, 624,
    600, 575, 549, 524, 499, 474, 448, 423, 399, 374, 350, 326, 303, 280, 258,
    236, 215, 195, 175, 157, 139, 122, 106, 91, 77, 64, 53, 42, 33, 24,
    17, 11, 7, 3, 1, 0, 0, 2, 5, 9, 14, 21, 28, 37, 47,
    58, 71, 84, 98, 114, 130, 148, 166, 185, 205, 225, 247, 269, 291, 314,
    338, 362, 386, 411, 436, 461, 486, 511
};

uint32_t DestAddress = (uint32_t) &(TIM2->CCR1);
uint32_t TIM3_Ticks = TIM3CLK / (NS * F_SIGNAL);
/* USER CODE END PV */

void SystemClock_Config(void);
static void MX_GPIO_Init(void);
static void MX_DMA_Init(void);
static void MX_SPI1_Init(void);
static void MX_USART2_UART_Init(void);
static void MX_I2C1_Init(void);
static void MX_TIM2_Init(void);
static void MX_TIM3_Init(void);
static void MX_TIM6_Init(void);
/* USER CODE BEGIN 0 */
int _write(int file, char *ptr, int len)
{
	HAL_UART_Transmit(&huart2, (uint8_t *)ptr, len, 1000);

	return len;
}
/* USER CODE END 0 */

/**
  * @brief  The application entry point.
  * @retval int
  */
int main(void)
{
  /* MCU Configuration--------------------------------------------------------*/

  /* Reset of all peripherals, Initializes the Flash interface and the Systick. */
  HAL_Init();

  /* Configure the system clock */
  SystemClock_Config();

  /* Initialize all configured peripherals */
  MX_GPIO_Init();
  MX_DMA_Init();
  MX_SPI1_Init();
  MX_USART2_UART_Init();
  MX_I2C1_Init();
  MX_TIM2_Init();
  MX_TIM3_Init();
  MX_TIM6_Init();
  /* Infinite loop */
  /* USER CODE BEGIN WHILE */
#if TEST_BAROMETER
  if (baro_init() < 0)
#else
  if (vario_init() < 0)
#endif
  {
	  printf("initialization failed!!\n");
  }


  HAL_TIM_PWM_Start(&htim2, TIM_CHANNEL_1);
  HAL_TIM_OC_Start(&htim3, TIM_CHANNEL_3);
  HAL_DMA_Start_IT(&hdma_tim3_ch3, (uint32_t)Wave_LUT, DestAddress, NS);
  __HAL_TIM_ENABLE_DMA(&htim3, TIM_DMA_CC3);

  HAL_TIM_Base_Start_IT(&htim6);

  uint32_t lastTick = HAL_GetTick();

  while (1)
  {
	  HAL_Delay(1);
  }

  while (1)
  {
#if TEST_BAROMETER
	  baro_measure();
	  HAL_Delay(1);
#if 0
		  printf("%.2f %.2f %.2f\n", baro_getPressure(), baro_getTemperature(), baro_getAltitude());
#else
		  printf("%.0f\n", baro_getAltitude() * 100);
#endif
#else
	  float v = vario_update();
	  HAL_Delay(10);
#endif

	  if (HAL_GetTick() - lastTick > 50)
	  {
		  printf("%.0f\n", v * 100);
		  lastTick = HAL_GetTick();
	  }

#if 0
	  // Case of BMP280(SPI)
	  {
		  HAL_GPIO_WritePin(CS2_GPIO_Port, CS2_Pin, GPIO_PIN_RESET);
		  uint8_t tx = 0xD0;
		  uint8_t rx = 0xFF;
		  HAL_SPI_Transmit(&hspi1, &tx, 1, 1000);
		  tx = 0x00;
		  HAL_SPI_TransmitReceive(&hspi1, &tx, &rx, 1, 1000);
		  HAL_GPIO_WritePin(CS2_GPIO_Port, CS2_Pin, GPIO_PIN_SET);
		  //HAL_Delay(1);
	  }
#endif

#if 0
	  // Case of MPU9560(SPI)
	  {
		  HAL_GPIO_WritePin(CS1_GPIO_Port, CS1_Pin, GPIO_PIN_RESET);
		  uint8_t tx = 0x75 | 0x80;
		  uint8_t rx = 0xFF;
		  HAL_SPI_Transmit(&hspi1, &tx, 1, 1000);
		  tx = 0x00;
		  HAL_SPI_TransmitReceive(&hspi1, &tx, &rx, 1, 1000);
		  HAL_GPIO_WritePin(CS1_GPIO_Port, CS1_Pin, GPIO_PIN_SET);
		  //HAL_Delay(1);
	  }
#endif

#if 0
	  // BMP280
	  {
		  uint16_t addr = (0x76 << 1);
		  uint8_t reg = 0xD0;
		  uint8_t value = 0;
		  HAL_I2C_Mem_Read(&hi2c1, addr, reg, 1, &value, 1, 1000);
		  //printf("%d\n", value);
	  }
#endif

#if 0
	  // MPU9560
	  {
		  uint16_t addr = (0x68 << 1);
		  uint8_t reg = 0x75;
		  uint8_t value = 0;
		  HAL_I2C_Mem_Read(&hi2c1, addr, reg, 1, &value, 1, 1000);
		  //printf("%d\n", value);
	  }
#endif


    /* USER CODE END WHILE */

    /* USER CODE BEGIN 3 */
  }
  /* USER CODE END 3 */
}

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
/* USER CODE BEGIN 4 */

void HAL_TIM_PeriodElapsedCallback(TIM_HandleTypeDef* htim)
{
	if (htim->Instance == TIM6)
	{
		HAL_GPIO_TogglePin(GPIOB, LED_R_Pin);
	}
}

/* USER CODE END 4 */
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
