akkdong/FlightComputer/src/Test/EInk4in2Test1/Core/Inc/main.h

#define RST_Pin GPIO_PIN_1
#define RST_GPIO_Port GPIOA
#define DC_Pin GPIO_PIN_2
#define DC_GPIO_Port GPIOA
#define BUSY_Pin GPIO_PIN_3
#define BUSY_GPIO_Port GPIOA
#define SPI_CS_Pin GPIO_PIN_4
#define SPI_CS_GPIO_Port GPIOA
