akkdong/FlightComputer/src/Test/EInk4in2Test1/Core/Src/main.c

/**
  ******************************************************************************
  * @file           : main.c
  * @brief          : Main program body
  ******************************************************************************
  * This notice applies to any and all portions of this file
  * that are not between comment pairs USER CODE BEGIN and
  * USER CODE END. Other portions of this file, whether 
  * inserted by the user or by software development tools
  * are owned by their respective copyright owners.
  *
  * Copyright (c) 2018 STMicroelectronics International N.V. 
  * All rights reserved.
  *
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
  ******************************************************************************
  */
/* Includes ------------------------------------------------------------------*/
#include "main.h"
#include "stm32f1xx_hal.h"
#include "spi.h"
#include "usart.h"
#include "usb_device.h"
#include "gpio.h"

/* USER CODE BEGIN Includes */
#include "epd4in2.h"
#include "epdif.h"
#include "epdpaint.h"
#include "imagedata.h"
#include "Page.h"
#include <stdlib.h>
#include <math.h>
/* USER CODE END Includes */


/* USER CODE BEGIN PV */

unsigned char frame[EPD_WIDTH * EPD_HEIGHT / 8];
char strBuf[32];
/* USER CODE END PV */

void SystemClock_Config(void);
static void MX_NVIC_Init(void);

/* USER CODE BEGIN PFP */

/* USER CODE END PFP */

/* USER CODE BEGIN 0 */


// Widget
//   position
//   size
//   data
//
// Widget_position : x, y
// Widget_size: w, h
// Widget_data: title, value
// Widget_data_title: const char *
// Widget_data_value: data pointer, data type(...), extra(precision, ... ??)
#if 1



/*
const char * Widget_GetLabel2(unsigned short id)
{
	switch (id)
	{
	case Widget_Empty :
		break;
	case Widget_Speed_Ground :
		return (const char *)"Speed (Km/h)";
	case Widget_Speed_Air :
	case Widget_Speed_Vertical :
		break;

	case Widget_Time_Flight :
	case Widget_Time_Current :
	case Widget_Date_Current :
		break;

	case Widget_Altitude_GPS :
		return "Altitude (m)";
	case Widget_Altitude_QNH :
	case Widget_Altitude_Takeoff :
	case Widget_Altitdue_Gain :
	case Widget_Altitude_Ref :

	case Widget_Heading :
	case Widget_Bearing :

	case Widget_LD :

	case Widget_Status_GPS :
	case Widget_Status_Battery :
	case Widget_Status_Date :
	case Widget_Status_Time :
	case Widget_Status_Bluetooth :
	case Widget_Status_Temperature :

	case Widget_Wind_Direction :
	case Widget_Wind_Speed :

	case Widget_G_VarioBar :
	case Widget_G_VarioHistory :
	case Widget_G_Heading :
	case Widget_G_Bearing :
	case Widget_G_North :
	case Widget_G_ThermalAssist :
		break;
	}

	return "";
}

const char * Widget_GetString2(unsigned short id)
{
	switch (id)
	{
	case Widget_Empty :
		break;
	case Widget_Speed_Ground :
		return "32";
	case Widget_Speed_Air :
	case Widget_Speed_Vertical :

	case Widget_Time_Flight :
	case Widget_Time_Current :
		return "10:33";
	case Widget_Date_Current :
		return "11/14";

	case Widget_Altitude_GPS :
		return "1450";
	case Widget_Altitude_QNH :
	case Widget_Altitude_Takeoff :
	case Widget_Altitdue_Gain :
	case Widget_Altitude_Ref :

	case Widget_Heading :
	case Widget_Bearing :

	case Widget_LD :

	case Widget_Status_GPS :
	case Widget_Status_Battery :
	case Widget_Status_Date :
	case Widget_Status_Time :
	case Widget_Status_Bluetooth :
	case Widget_Status_Temperature :

	case Widget_Wind_Direction :
	case Widget_Wind_Speed :

	case Widget_G_VarioBar :
	case Widget_G_VarioHistory :
	case Widget_G_Heading :
	case Widget_G_Bearing :
	case Widget_G_North :
	case Widget_G_ThermalAssist :
		break;
	}

	return "";
}

void * Widget_GetDataPtr2(unsigned short id)
{
	switch (id)
	{
	case Widget_Empty :
	case Widget_Speed_Ground :
	case Widget_Speed_Air :
	case Widget_Speed_Vertical :

	case Widget_Time_Flight :
	case Widget_Time_Current :
	case Widget_Date_Current :

	case Widget_Altitude_GPS :
	case Widget_Altitude_QNH :
	case Widget_Altitude_Takeoff :
	case Widget_Altitdue_Gain :
	case Widget_Altitude_Ref :

	case Widget_Heading :
	case Widget_Bearing :

	case Widget_LD :

	case Widget_Status_GPS :
	case Widget_Status_Battery :
	case Widget_Status_Date :
	case Widget_Status_Time :
	case Widget_Status_Bluetooth :
	case Widget_Status_Temperature :

	case Widget_Wind_Direction :
	case Widget_Wind_Speed :

	case Widget_G_VarioBar :
	case Widget_G_VarioHistory :
	case Widget_G_Heading :
	case Widget_G_Bearing :
	case Widget_G_North :
	case Widget_G_ThermalAssist :
		break;
	}

	return 0;
}

void Widget_DrawLabel(Widget * this, Paint * paint)
{
	// erase bkground
	Paint_DrawFilledRectangle(paint, this->x, this->y, this->x + this->w - 0, this->y + this->h - 0, COLORED);
	// draw frame
	//Paint_DrawRectangle(paint, this->x, this->y, this->x + this->w - 1, this->y + this->h - 1, COLORED);

	// draw value
	const char * value = Widget_GetString(this->cId);
	int x = this->x + 2;
	int y = this->y + 2;
	Paint_DrawStringAt(paint, x, y, value, &Font12, UNCOLORED);
}

void Widget_DrawText(Widget * this, Paint * paint)
{
	// erase background
	Paint_DrawFilledRectangle(paint, this->x, this->y, this->x + this->w - 0, this->y + this->h - 0, UNCOLORED);
	// draw frame
	Paint_DrawRectangle(paint, this->x, this->y, this->x + this->w - 0, this->y + this->h - 0, COLORED);

	// draw label
	const char * label = Widget_GetLabel(this->cId);
	int x = this->x + 2;
	int y = this->y + 2;
	if (label)
		Paint_DrawStringAt(paint, x, y, label, &Font12, COLORED);

	// draw value
	const char * value = Widget_GetString(this->cId);
	x = this->x + this->w - (Font24.Width * strlen((char *)value));
	y = y + 12;
	Paint_DrawStringAt(paint, x, y, value, &Font24, COLORED);
}
*/


#endif


/**
  * @brief  EXTI line detection callbacks.
  * @param  GPIO_Pin: Specifies the pins connected EXTI line
  * @retval None
  */


volatile int pressed = 0;
volatile uint32_t tick;
volatile uint32_t tickPress;

void HAL_GPIO_EXTI_Callback(uint16_t GPIO_Pin)
{
	tickPress = tick = HAL_GetTick();
	pressed = 1;
}

void goStandbyMode()
{
	  /* Enable Power Clock*/
	  //__HAL_RCC_PWR_CLK_ENABLE();

	  /* Allow access to Backup */
	  //HAL_PWR_EnableBkUpAccess();

	  /* Reset RTC Domain */
	  //__HAL_RCC_BACKUPRESET_FORCE();
	  //__HAL_RCC_BACKUPRESET_RELEASE();

	  /* Disable all used wake-up sources: Pin1(PA.0) */
	  HAL_PWR_DisableWakeUpPin(PWR_WAKEUP_PIN1);

	  /* Clear all related wake-up flags */
	  __HAL_PWR_CLEAR_FLAG(PWR_FLAG_WU);

	  /* Re-enable all used wake-up sources: Pin1(PA.0) */
	  HAL_PWR_EnableWakeUpPin(PWR_WAKEUP_PIN1);

	  /* Request to enter STANDBY mode  */
	  HAL_PWR_EnterSTANDBYMode();

	  /* This code will never be reached! */
	  while (1)
	  {
	  }
}

/* USER CODE END 0 */

/**
  * @brief  The application entry point.
  *
  * @retval None
  */
int main(void)
{
  /* USER CODE BEGIN 1 */
	unsigned char* frame_buffer = frame; // (unsigned char*)malloc(EPD_WIDTH * EPD_HEIGHT / 8);
  /* USER CODE END 1 */

  /* MCU Configuration----------------------------------------------------------*/

  /* Reset of all peripherals, Initializes the Flash interface and the Systick. */
  HAL_Init();

  /* Configure the system clock */
  SystemClock_Config();

  /* Initialize all configured peripherals */
  MX_GPIO_Init();
  MX_USART1_UART_Init();
  MX_USB_DEVICE_Init();
  MX_SPI1_Init();

  /* Initialize interrupts */
  MX_NVIC_Init();
  /* USER CODE BEGIN 2 */
  if (__HAL_PWR_GET_FLAG(PWR_FLAG_SB) != RESET)
  {
    /* Clear Standby flag */
    __HAL_PWR_CLEAR_FLAG(PWR_FLAG_SB);
  }

  printf("EInk4in2 Test start...\n");

  pressed = 0;
  tick = HAL_GetTick();

  while (1)
  {
	  if (! pressed)
	  {
		  if ((HAL_GetTick() - tick) > 500)
		  {
			  HAL_GPIO_TogglePin(GPIOD, GPIO_PIN_2);
			  tick = HAL_GetTick();
		  }
	  }
	  else
	  {
		  if ((HAL_GetTick() - tickPress) > 200)
		  {
			  HAL_GPIO_TogglePin(GPIOD, GPIO_PIN_2);
			  tickPress = HAL_GetTick();
		  }

		  if (HAL_GPIO_ReadPin(GPIOA, GPIO_PIN_0) == GPIO_PIN_RESET)
		  {
			  if ((HAL_GetTick() - tick) > 2000)
			  {
				 for (int i = 0; i < 10; i++)
				 {
					 HAL_GPIO_TogglePin(GPIOD, GPIO_PIN_2);
					 HAL_Delay(100);
				 }

				 HAL_GPIO_WritePin(GPIOD, GPIO_PIN_2, GPIO_PIN_RESET);
				 HAL_Delay(1000);

				 goStandbyMode();
			  }
			  else
			  {
				  pressed = 0;
			  }
		  }
	  }
  }




  EPD epd;
  if (EPD_Init(&epd) != 0) {
    printf("e-Paper init failed\n");
    return -1;
  }

  //
  EPD_ClearFrame(&epd);
  EPD_DisplayFrame(&epd);

  //
  Paint paint;
  Paint_Init(&paint, frame_buffer, epd.width, epd.height);
  Paint_Clear(&paint, UNCOLORED);

#if 0
#if 1

	Paint_DrawFilledCircle(&paint, 32, 32, 8, COLORED);
	EPD_SetPartialWindow(&epd, Paint_GetImage(&paint), 0, 0, Paint_GetWidth(&paint), Paint_GetHeight(&paint),2);
	EPD_DisplayFrameQuick(&epd);
	EPD_WaitUntilIdle(&epd);

	Paint_DrawFilledCircle(&paint, 16, 16, 8, COLORED);
	EPD_SetPartialWindow(&epd, Paint_GetImage(&paint), 0, 0, Paint_GetWidth(&paint), Paint_GetHeight(&paint),2);
	EPD_DisplayFrameQuick(&epd);
	EPD_WaitUntilIdle(&epd);

	Paint_DrawFilledCircle(&paint, 40, 32, 18, COLORED);
	EPD_SetPartialWindow(&epd, Paint_GetImage(&paint), 0, 0, Paint_GetWidth(&paint), Paint_GetHeight(&paint),2);
	EPD_DisplayFrameQuick(&epd);
	EPD_WaitUntilIdle(&epd);

	Paint_DrawFilledCircle(&paint, 64, 64, 24, COLORED);
	EPD_SetPartialWindow(&epd, Paint_GetImage(&paint), 0, 0, Paint_GetWidth(&paint), Paint_GetHeight(&paint),2);
	EPD_DisplayFrameQuick(&epd);
	EPD_WaitUntilIdle(&epd);

	Paint_DrawFilledCircle(&paint, 200, 150, 50, COLORED);
	EPD_SetPartialWindow(&epd, Paint_GetImage(&paint), 0, 0, Paint_GetWidth(&paint), Paint_GetHeight(&paint),2);
	EPD_DisplayFrameQuick(&epd);
	EPD_WaitUntilIdle(&epd);

	Paint_DrawFilledCircle(&paint, 250, 75, 80, COLORED);
	EPD_SetPartialWindow(&epd, Paint_GetImage(&paint), 0, 0, Paint_GetWidth(&paint), Paint_GetHeight(&paint),2);
	EPD_DisplayFrameQuick(&epd);
	EPD_WaitUntilIdle(&epd);

	Paint_DrawFilledCircle(&paint, 100, 250, 80, COLORED);
	EPD_SetPartialWindow(&epd, Paint_GetImage(&paint), 0, 0, Paint_GetWidth(&paint), Paint_GetHeight(&paint),2);
	EPD_DisplayFrameQuick(&epd);
	EPD_WaitUntilIdle(&epd);

	Paint_DrawFilledCircle(&paint, 100, 250, 50, UNCOLORED);
	EPD_SetPartialWindow(&epd, Paint_GetImage(&paint), 0, 0, Paint_GetWidth(&paint), Paint_GetHeight(&paint),2);
	EPD_DisplayFrameQuick(&epd);
	EPD_WaitUntilIdle(&epd);
	Paint_DrawFilledCircle(&paint, 250, 75, 50, UNCOLORED);
	EPD_SetPartialWindow(&epd, Paint_GetImage(&paint), 0, 0, Paint_GetWidth(&paint), Paint_GetHeight(&paint),2);
	EPD_DisplayFrameQuick(&epd);
	EPD_WaitUntilIdle(&epd);

	Paint_DrawFilledCircle(&paint, 200, 150, 20, UNCOLORED);
	EPD_SetPartialWindow(&epd, Paint_GetImage(&paint), 0, 0, Paint_GetWidth(&paint), Paint_GetHeight(&paint),2);
	EPD_DisplayFrameQuick(&epd);
	EPD_WaitUntilIdle(&epd);
	EPD_DelayMs(&epd, 3000);

	Paint_Clear(&paint, UNCOLORED);
	EPD_DisplayFrame(&epd);

	//
	float phase = 0.0;
	float twopi = 3.14159 * 2;

	static char outstr[15];
	while(phase < 8)
	{
		Paint_Clear(&paint, UNCOLORED);
		Paint_DrawStringAt(&paint, (int)30+phase*10, 30, itoa(phase * 10, outstr, 10), &Font24, COLORED);
		Paint_DrawFilledCircle(&paint, 200+80*sin(phase), 150+80*cos(phase), 20, COLORED);
		EPD_SetPartialWindow(&epd, Paint_GetImage(&paint), 0, 0, Paint_GetWidth(&paint), Paint_GetHeight(&paint),2);
		EPD_DisplayFrameQuick(&epd);
		EPD_WaitUntilIdle(&epd);
		phase = phase + 0.2;
	}

	for(int i = 0; i<2;i++)
	{
		Paint_Clear(&paint, UNCOLORED);
		EPD_SetPartialWindow(&epd, Paint_GetImage(&paint), 0, 0, Paint_GetWidth(&paint), Paint_GetHeight(&paint),2);
		EPD_DisplayFrame(&epd);
		EPD_DelayMs(&epd, 10);
	}

	/* This displays an image */
	EPD_DisplayFrameEx(&epd, IMAGE_BUTTERFLY);
	EPD_DelayMs(&epd, 4000);
	EPD_DisplayFrameEx(&epd, IMAGE_ASCIENCE);
	EPD_DelayMs(&epd, 4000);
	EPD_DisplayFrameEx(&epd, IMAGE_PLAYBUTTON);
	/* Deep sleep */
	EPD_Sleep(&epd);

#else
  /* Draw something to the frame_buffer */
  /* For simplicity, the arguments are explicit numerical coordinates */
  Paint_DrawRectangle(&paint, 20, 80, 180, 280, COLORED);
  Paint_DrawLine(&paint, 20, 80, 180, 280, COLORED);
  Paint_DrawLine(&paint, 180, 80, 20, 280, COLORED);
  Paint_DrawFilledRectangle(&paint, 200, 80, 360, 280, COLORED);
  Paint_DrawCircle(&paint, 300, 160, 60, UNCOLORED);
  Paint_DrawFilledCircle(&paint, 90, 210, 30, COLORED);

  /*Write strings to the buffer */
  Paint_DrawFilledRectangle(&paint, 0, 6, 400, 30, COLORED);
  Paint_DrawStringAt(&paint, 100, 10, "Hello world!", &Font24, UNCOLORED);
  Paint_DrawStringAt(&paint, 100, 40, "e-Paper Demo", &Font24, COLORED);

  /* Display the frame_buffer */
  EPD_DisplayFrameEx(&epd, frame_buffer);

  /* Display the image buffer */
  EPD_DisplayFrameEx(&epd, IMAGE_BUTTERFLY);
#endif
#endif
  /* USER CODE END 2 */

  /* Infinite loop */
  /* USER CODE BEGIN WHILE */
  /*
  int graph[50];
  int sOffset = 0;
  int y1, y2;
  int x, y, w, h;
  uint32_t tick = HAL_GetTick();

  for (int i = 0; i < 50; i++)
	  graph[i] = 60;
	*/

  Paint_DrawFilledRectangle(&paint, 0, 0, 399, 299, UNCOLORED);


  while (1)
  {
#if 0
	  // area1 (0,0) - (200,150)
	  Paint_DrawFilledRectangle(&paint, 0, 0, 200, 150, UNCOLORED);
	  Paint_DrawRectangle(&paint, 0, 0, 200, 150, COLORED);
	  graph[sOffset] = rand() % 100;
	  sOffset = (sOffset + 1) % 50;
	  y1 = graph[sOffset] + 25;
	  for (int i = 1; i < 50; i++)
	  {
		  int j = (sOffset + i) % 50;
		  y2 = graph[j] + 25;
		  Paint_DrawLine(&paint, (i - 1) * 4, y1, i * 4, y2, COLORED);
		  y1 = y2;
	  }

	  // area2 (200,0) - (400,150)
	  Paint_DrawFilledRectangle(&paint, 200, 0, 400, 150, UNCOLORED);
	  Paint_DrawRectangle(&paint, 200, 0, 400, 150, COLORED);
	  Paint_DrawFilledCircle(&paint, 300, 75, rand() % 50 + 10, COLORED);


	  // area3 (0,150) - (200,300)
	  Paint_DrawFilledRectangle(&paint, 0, 150, 200, 300, UNCOLORED);
	  Paint_DrawRectangle(&paint, 0, 150, 200, 300, COLORED);
	  Paint_DrawCircle(&paint, 100, 225, rand() % 50 + 10, COLORED);

	  // area4 (200,15) - (400,300)
	  /*
	  Paint_DrawFilledRectangle(&paint, 200, 150, 400, 300, UNCOLORED);
	  Paint_DrawRectangle(&paint, 200, 150, 400, 300, COLORED);

	  itoa(HAL_GetTick(), strBuf, 10);
	  Paint_DrawStringAt(&paint, 260, 210, strBuf, &Font24, COLORED);
	  */

	  // 5x8 * 10 = 50x8
	  // 7x12 * 10 = 70x12
	  // 17x24 * 5 = 85x24
	  // w = 85 + 1 + 1 = 87
	  // h = 1 + 12 + 24 + 1 = 38
	  x = 210; y = 155;
	  Paint_DrawRectangle(&paint, x, y, x+ 87, y+ 38, COLORED);
	  Paint_DrawStringAt(&paint, x+1, y+1, "Speed Km/h", &Font12, COLORED);
	  Paint_DrawStringAt(&paint, x+1, y+14, "   32", &Font24, COLORED);

	  x = 210; y = 155 + 38;
	  Paint_DrawRectangle(&paint, x, y, x+ 87, y+ 38, COLORED);
	  Paint_DrawStringAt(&paint, x+1, y+1, "Altitude m", &Font12, COLORED);
	  Paint_DrawStringAt(&paint, x+1, y+14, " 1702", &Font24, COLORED);
#else
	  /*
	  //
	  //Paint_DrawFilledRectangle(&paint, 0, 0, 399, 299, UNCOLORED);

	  //
	  x = 0; y = 0;
	  Paint_DrawStringAt(&paint, x, y, "2018-11-12 ", &Font12, COLORED);
	  x = x + 11 * 7; y = 0;
	  Paint_DrawStringAt(&paint, x, y, "08:10 ", &Font12, COLORED);
	  x = x + 6 * 7; y = 0;
	  Paint_DrawStringAt(&paint, x, y, "98%", &Font12, COLORED);

	  //
	  x = 0; y = 12; w = 90; h = 38;
	  //Paint_DrawRectangle(&paint, x, y, x + w, y + h, COLORED);
	  Paint_DrawStringAt(&paint, x+1, y+1, "Altitude (m)", &Font12, COLORED);
	  Paint_DrawStringAt(&paint, x+1, y+14, "1702  ", &Font24, COLORED);

	  x = 0; y = y + h;
	  sprintf((char *)graph, "%d", (HAL_GetTick() - tick) / 100);
	  Paint_DrawFilledRectangle(&paint, x + 1, y + 1, x + w - 2, y + h - 2, UNCOLORED);
	  Paint_DrawStringAt(&paint, x+1, y+1, "Speed Km/h", &Font12, COLORED);
	  x += Font24.Width * (5 - strlen((char *)graph));
	  Paint_DrawStringAt(&paint, x+1, y+14, graph, &Font24, COLORED);
	  */

	  //for (int i = 0; i < sizeof(_widget) / sizeof(_widget[0]); i++)
	  //{
	  //	  Widget_Draw(&_widget[i], &paint);
	  //}
	  Page_Draw(0, &paint);

#endif

	  //
	  uint32_t tickStart = HAL_GetTick();
	  EPD_SetPartialWindow(&epd, Paint_GetImage(&paint), 0, 0, Paint_GetWidth(&paint), Paint_GetHeight(&paint),2);
	  EPD_DisplayFrameQuick(&epd);
	  printf("refresh screen: %lu\n", HAL_GetTick() - tickStart);

	  EPD_DelayMs(&epd, 500);

  /* USER CODE END WHILE */

  /* USER CODE BEGIN 3 */

  }
  /* USER CODE END 3 */

}

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
/* USER CODE BEGIN 4 */

#ifdef __cplusplus
 extern "C" {
#endif

int __io_putchar(int ch) {
  HAL_UART_Transmit(&huart1, (uint8_t *)&ch, 1, 0xFFFF);
  return ch;
}

int _write(int file, char *ptr, int len)
{
  /* Implement your write code here, this is used by puts and printf for example */
  int i=0;
  for(i=0 ; i<len ; i++)
	  HAL_UART_Transmit(&huart1, (uint8_t *)&ptr[i], 1, 0xFFFF);
	  //ITM_SendChar((*ptr++));
  return len;
}

#ifdef __cplusplus
}
#endif

/* USER CODE END 4 */
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
