akkdong/FlightComputer/src/Test/EInk4in2Test1/BSP/epd4in2.h

/**
 *  @filename   :   epd4in2.h
 *  @brief      :   Header file for Dual-color e-paper library epd4in2.c
 *  @author     :   Yehui from Waveshare
 *  
 *  Copyright (C) Waveshare     August 2 2017
 *
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
 * THE SOFTWARE IS PROVIDED "AS IS", WITHOUT WARRANTY OF ANY KIND, EXPRESS OR
 * IMPLIED, INCLUDING BUT NOT LIMITED TO THE WARRANTIES OF MERCHANTABILITY,
 * FITNESS OR A PARTICULAR PURPOSE AND NONINFRINGEMENT. IN NO EVENT SHALL THE
 * AUTHORS OR COPYRIGHT HOLDERS BE LIABLE FOR ANY CLAIM, DAMAGES OR OTHER
 * LIABILITY WHETHER IN AN ACTION OF CONTRACT, TORT OR OTHERWISE, ARISING FROM,
 * OUT OF OR IN CONNECTION WITH THE SOFTWARE OR THE USE OR OTHER DEALINGS IN
 * THE SOFTWARE.
 */

#ifndef EPD4IN2_H
#define EPD4IN2_H

#include "fonts.h"

// Display resolution
#define EPD_WIDTH       400
#define EPD_HEIGHT      300

// EPD4IN2 commands
#define PANEL_SETTING                               0x00
#define POWER_SETTING                               0x01
#define POWER_OFF                                   0x02
#define POWER_OFF_SEQUENCE_SETTING                  0x03
#define POWER_ON                                    0x04
#define POWER_ON_MEASURE                            0x05
#define BOOSTER_SOFT_START                          0x06
#define DEEP_SLEEP                                  0x07
#define DATA_START_TRANSMISSION_1                   0x10
#define DATA_STOP                                   0x11
#define DISPLAY_REFRESH                             0x12
#define DATA_START_TRANSMISSION_2                   0x13
#define LUT_FOR_VCOM                                0x20 
#define LUT_WHITE_TO_WHITE                          0x21
#define LUT_BLACK_TO_WHITE                          0x22
#define LUT_WHITE_TO_BLACK                          0x23
#define LUT_BLACK_TO_BLACK                          0x24
#define PLL_CONTROL                                 0x30
#define TEMPERATURE_SENSOR_COMMAND                  0x40
#define TEMPERATURE_SENSOR_SELECTION                0x41
#define TEMPERATURE_SENSOR_WRITE                    0x42
#define TEMPERATURE_SENSOR_READ                     0x43
#define VCOM_AND_DATA_INTERVAL_SETTING              0x50
#define LOW_POWER_DETECTION                         0x51
#define TCON_SETTING                                0x60
#define RESOLUTION_SETTING                          0x61
#define GSST_SETTING                                0x65
#define GET_STATUS                                  0x71
#define AUTO_MEASUREMENT_VCOM                       0x80
#define READ_VCOM_VALUE                             0x81
#define VCM_DC_SETTING                              0x82
#define PARTIAL_WINDOW                              0x90
#define PARTIAL_IN                                  0x91
#define PARTIAL_OUT                                 0x92
#define PROGRAM_MODE                                0xA0
#define ACTIVE_PROGRAMMING                          0xA1
#define READ_OTP                                    0xA2
#define POWER_SAVING                                0xE3

extern const unsigned char lut_vcom0[];
extern const unsigned char lut_ww[];
extern const unsigned char lut_bw[];
extern const unsigned char lut_bb[];
extern const unsigned char lut_wb[];

extern const unsigned char lut_vcom0_quick[];
extern const unsigned char lut_ww_quick[];
extern const unsigned char lut_bw_quick[];
extern const unsigned char lut_bb_quick[];
extern const unsigned char lut_wb_quick[];

typedef struct EPD_t {
  int reset_pin;
  int dc_pin;
  int cs_pin;
  int busy_pin;
  int width;
  int height;
} EPD;

/* Hardware operating functions */
int  EPD_Init(EPD* epd);
void EPD_WaitUntilIdle(EPD* epd);
void EPD_DelayMs(EPD* epd, unsigned int delay_time);
void EPD_Reset(EPD* epd);
void EPD_SetPartialWindow(EPD* epd, const unsigned char* buffer_black, int x, int y, int w, int l, int dtm);
void EPD_DisplayFrameEx(EPD* epd, const unsigned char* frame_buffer_black);
void EPD_DisplayFrame(EPD* epd);
void EPD_DisplayFrameQuick(EPD* epd);
void EPD_ClearFrame(EPD* epd);
void EPD_Sleep(EPD* epd);
void EPD_DigitalWrite(EPD* epd, int pin, int value);
int  EPD_DigitalRead(EPD* epd, int pin);
void EPD_SendCommand(EPD* epd, unsigned char command);
void EPD_SendData(EPD* epd, unsigned char data);
void EPD_SetLut(EPD* epd);
void EPD_SetLutQuick(EPD* epd);
#endif /* EPD4IN2_H */

/* END OF FILE */
