akkdong/FlightComputer/src/Test/GY91-Test/Drivers/MPU9250/MPU9250_Config.h

/*
 * MPU9250_Config.h
 *
 *  Created on: Feb 28, 2019
 *      Author: Desert
 */

#ifndef UTIL_MPU9250_CONFIG_H_
#define UTIL_MPU9250_CONFIG_H_

#define MPU9250_SPI			hspi1
#define	MPU9250_CS_GPIO		IMU_GPIO_Port
#define	MPU9250_CS_PIN		IMU_Pin

#endif /* UTIL_MPU9250_CONFIG_H_ */
